maxime-leblan/Projet-E3-2026-ESIEE-Paris/Rapport/Exemple de document LateX/Code_TIPE/main.pdf

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

7 | mot = ""
8
9 | for i in range ( taille_mot - 1 , 0 , -1) :
10 | diviseur = b ** i
11 | quotient = dividende // diviseur
12 | mot += liste_int_a_char [ quotient ]
13 | dividende -= quotient * diviseur
14 | mot += liste_int_a_char [ dividende % b ]
15
16 | return mot
17
18 # Cré ation de l'exception " InvNotFound " utile dans la suite
19 | class InvNotFound ( Exception ) :
20 | pass
| Diapositive 38
1 | def inverse_mod ( b : int , n : int ) :
2 | """ Fonction qui prend en param ètre deux entiers b et n et renvoie l'
| inverse de b modulo n (ie b^( -1))
3 | ou bien renvoie l'erreur 'InvNotFound ' si b^( -1) n'existe pas """
4 | n_0 = n
5 | b_0 = b
6 | t_0 = 0
7 | t = 1
8 | q = int ( n_0 / b_0 )
9 | r = n_0 - q * b_0
10 | while r > 0:
11 | temp = t_0 - q * t
12 | if temp >= 0:
13 | temp = temp % n
14 | else :
15 | temp = n - (( - temp ) % n )
16 | t_0 = t
17 | t = temp
18 | n_0 = b_0
19 | b_0 = r
20 | q = int( n_0 / b_0 )
21 | r = n_0 - q * b_0
22 | if b_0 != 1:
23 | raise InvNotFound ()
24 | else :
25 | return t
| Diapositive 39
1 | def creation_cles ( lst_nb_prem : list ) :
2 | """ Fonction prenant en param ètre une liste de nombres premiers et qui crée
| puis renvoie un couple de la forme
3 | ( cle_publique , cle_privee ) en suivant la mé thode de cré ation des clés de l
| 'algorithme de chiffrement RSA\n
4 | - cle_publique : tuple int \n
5 | - cle_privee : int """
6 | e = 2
7 | # On choisit alé atoirement les valeurs de p et q distinctes
8 | p = lst_nb_prem . pop ( rd . randint (0 , len ( lst_nb_prem ) - 1) )
9 | q = rd . choice ( lst_nb_prem )
10 | # On choisit e et phi_n

11 | n = p * q
12 | phi_n = ( p - 1) * ( q - 1)
13
14 | for i in range (2 , phi_n ) : # on cherche le premier e qui convient en partant
| de e = 2
15 | if fu . pgcd (i , phi_n ) == 1:
16 | e = i
17 | break
18 | d = inverse_mod (e , phi_n )
19
20 | return (( n , e ) , d ) # on renvoie (clé publique , clé priv ée)
| Diapositive 40
1 | def chiffrer_RSA_naif ( m : int , cle_pb : tuple ) :
2 | """ Fonction qui prend en param ètre un entier m qui correspond au message à
| chiffrer et un tuple cle_pb qui
3 | correspond à la clé de chiffrement . Elle renvoie un entier correspondant au
| message chiffr é """
4
5 | assert ( m < cle_pb [0])
6 | # print ("début calcul chiffrement et cle_pb : " , cle_pb )
7 | reste = 1
8 | for _ in range ( cle_pb [1]) :
9 | reste *= m
10 | reste = reste % cle_pb [0]
11 | return reste
12
13 | def chiffrer_RSA_v2 ( m : int , cle_pb : tuple ) :
14 | """ Fonction qui prend en param ètre un entier m qui correspond au message à
| chiffrer et un tuple cle_pb qui
15 | correspond à la clé de chiffrement . Elle renvoie un entier correspondant au
| message chiffr é """
16
17 | assert ( m < cle_pb [0])
18 | return modulo_exp (m , cle_pb [1] , cle_pb [0])
| Diapositive 41
1 | def dechiffrer_RSA_naif ( x : int , cle_pv : int , n : int) :
2 | """ Fonction prenant en param ètre un entier x correspondant au message à dé
| chiffrer , cle_pv un entier
3 | correspondant à la clé de dé chiffrement et n issue de la cle de chiffrement
| du message . Elle renvoie un entier
4 | correspondant au message dé chiffr é """
5
6 | reste = 1
7 | for _ in range ( cle_pv ) :
8 | reste *= x
9 | reste = reste % n
10
11 | return reste
12
13 | def dechiffrer_RSA_v2 ( x : int , cle_pv : int , n : int) :
14 | """ Fonction prenant en param ètre un entier x correspondant au message à dé
| chiffrer , cle_pv un entier
15 | correspondant à la clé de dé chiffrement et n issue de la cle de chiffrement
| du message . Elle renvoie un entier

16 | correspondant au message dé chiffr é """
17
18 | return modulo_exp (x , cle_pv , n )
| Diapositive 42
1 | def chiffrer_chaine_RSA ( chaine :str , cle_pb :tuple , taille_facteur = -1) :
2 | """ Fonction qui prend en param ètre une chaine de caract ères 'chaine ' et un
| tuple 'cle_pb ' et renvoie
3 | une liste d'entiers correspondants aux facteurs de taille ' taille_facteur ',
| chiffr és avec la fonction ' chiffrer_RSA (...) ',
4 | dont la concat é nation forme la chaine 'chaine ' avant son chiffrement """
5 | if taille_facteur == ( -1) :
6 | taille_facteur = len ( chaine )
7 | chaine_chiffree = []
8 | chaine_fractionnee = []
9 | chaine_courante = ""
10
11 | for i in range (len( chaine ) ) : # On dé compose 'chaine ' en une liste de
| facteurs de taille ' taille_facteur '
12 | chaine_courante += chaine [ i ]
13 | if len( chaine_courante ) % taille_facteur == 0:
14 | chaine_fractionnee . append ( chaine_courante )
15 | chaine_courante = ""
16
17 | if chaine_courante != "":
18 | for i in range (len( chaine_courante ) , taille_facteur ) : # on ajoute des
| espaces pour que le dernier facteur soit de taille taille_facteur
19 | chaine_courante += " "
20 | chaine_fractionnee . append ( chaine_courante ) # on ajoute le dernier
| facteur de taille < ' taille_facteur ' ( sans compter les espaces )
21
22 | for facteur in chaine_fractionnee : # On chiffre tous les facteurs avec la
| fonction ' chiffrer_RSA (...) '
23 | int_facteur_courant = string_to_int ( facteur , base =95)
24 | chaine_chiffree . append ( chiffrer_RSA_v2 ( int_facteur_courant , cle_pb ) )
25 | return chaine_chiffree
| Diapositive 43
1 | def dechiffrer_chaine_RSA ( liste :list , cle_pv : int , n : int , taille_entiers =1) :
2 | """ Fonction qui prend en param ètre une liste d'entiers 'liste ', un entier
| 'cle_pv ' et un entier n et
3 | renvoie la concat é nation des chaines de caract ères dé chiffr ées avec '
| dechiffrer_RSA (...) ' à partir des entiers
4 | contenu dans 'liste ' repr é sentant des chaines de caract è res de taille '
| taille_entiers ' """
5
6 | chaine_dechiffree = ""
7
8 | for i in range (len( liste ) ) : # On dé chiffre tous les termes de liste sauf le
| dernier
9 | chaine_courante = int_to_string ( dechiffrer_RSA_v2 ( liste [ i ] , cle_pv , n ) ,
| taille_entiers , b =95)
10 | chaine_dechiffree += chaine_courante
11
12 | return chaine_dechiffree

Diapositive 44

1 | def aux_bytesub ( a : str) :
2 | """ Fonction auxiliaire de bytesub qui prend en entr ée un élé ment codé en
| hexad é cimal et renvoie le ré sultat
3 | de la fonction ByteSub appliqu ée à celui -ci """
4
5 | # on construit b_prime = GF(a)
6 | m_gf_i = m_gf_hex_a_dec [ a [0]]
7 | m_gf_j = m_gf_hex_a_dec [ a [1]]
8 | b_prime = MATRICE_GF [ m_gf_i ][ m_gf_j ]
9 | # on construit b à partir de b_prime
10 | b_prime = int( b_prime , 16)
11 | b_prime = str(bin( b_prime ) )
12 | b_prime = b_prime [2:]
13 | b_prime = fu . remplir_zeros ( b_prime , 8)
14 | b_prime = [[ int( b_prime [ i ]) ] for i in range (len( b_prime ) ) ]
15 | b = fu . produit_matriciel ( mat_f1 , b_prime , ( len ( mat_f1 ) , len( mat_f1 ) ) , (len(
| b_prime ) , 1) )
16 | b = fu . somme_matricielle (b , mat_f2 , len( mat_f2 ) , 1)
17 | for i in range (len( b ) ) :
18 | b [ i ][0] = b [ i ][0] % 2
19 | b_final = ""
20 | for chiffre in b :
21 | b_final += str( chiffre [0])
22 | b_final = fu . remplir_zeros ( b_final , 8)
23 | b_final = fu . bin_vers_dec ( b_final )
24 | b_final = str(hex( b_final ) )
25
26 | return b_final [2:]
| Diapositive 45
1 | def bytesub ( matrice : list [ list ]) :
2 | """ Fonction bytesub qui prend en entr ée une matrice cod ée en hexad é cimal
| et renvoie le ré sultat
3 | de la fonction aux_bytesub de AES appliqu ée à celle -ci """
4
5 | return [[ aux_bytesub ( matrice [ i ][ j ]) for j in range (len ( matrice ) ) ] for i in
| range (len( matrice ) ) ]
6
7 | def shiftrows ( matrice : list [ list ]) :
8 | """ Fonction qui applique la fonction ShiftRows de AES sur la matrice """
9 | n = len ( matrice )
10 | matrice_finale = []
11 | for d in range ( n ) :
12 | matrice_finale . append ( fu . decale_liste ( matrice [ d ] , d ) )
13
14 | return matrice_finale
| Diapositive 46

1 # Algorithme AES impl é ment é avec une biblioth èque
2 | def chiffrer_AES ( message :str , cle : bytes , vecteur : bytes ) :
3 | """ Fonction qui prend en param ètre un message , une clé et un vecteur et
| renvoie une chaine de
4 | caract ère correspondant au chiffrement de 'message ' avec l'algorithme AES
| en utilisant la clé 'cle '

5 | et le vecteur d' initialisation 'vecteur '\n
6 | - message : chaine de caract ères \n
7 | - cle : chaine de caract è res sur 32 octets \n
8 | - vecteur : chaine de caract ères sur 16 octets """
9
10 | padder = padding . PKCS7 (128) . padder ()
11 | padded_data = padder . update ( message . encode ('utf -8 ') )
12 | padded_data += padder . finalize ()
13
14 | cipher = Cipher ( algorithms . AES ( cle ) , modes . CBC ( vecteur ) , backend =
default_backend () )
15 | encryptor = cipher . encryptor ()
16 | message_chiffre = encryptor . update ( padded_data ) + encryptor . finalize ()
17
18 | return message_chiffre

Diapositive 47

1 | def dechiffrer_AES ( message_chiffre , cle : bytes , vecteur : bytes ) :
2 | """ Fonction qui prend en param ètre un message , une clé et un vecteur et
renvoie une chaine de
3 | caract ère correspondant au dé chiffrement de ' message_chiffre ' avec l'
algorithme AES en utilisant la clé 'cle '
4 | et le vecteur d' initialisation 'vecteur '\n
5 | - message_chiffre : chaine de caract ères\n
6 | - cle : chaine de caract è res sur 32 octets \n
7 | - vecteur : chaine de caract ères sur 16 octets """
8
9 | decryptor = Cipher ( algorithms . AES ( cle ) , modes . CBC ( vecteur ) , backend =
default_backend () ) . decryptor ()
10 | decrypted_data = decryptor . update ( message_chiffre ) + decryptor . finalize ()
11
12 | unpadder = padding . PKCS7 (128) . unpadder ()
13 | unpadded_data = unpadder . update ( decrypted_data )
14 | unpadded_data += unpadder . finalize ()
15
16 | return unpadded_data . decode ('utf -8 ')

Diapositive 48

3 | serveur.py
1 | class Serveur :
2 | """ Classe permettant de simuler un serveur informatique simplifi é à l'aide
du module socket """
3
4 | def __init__ ( self , modele :int , port =6390) :
5 | self . host = ""
6 | self . port = port
7 | self . socket = None
8 | self . clients = []
9 | self . threads = {}
10 | self . id_client = 1
11 | self . arret = False
12 | self . modele = modele
13
14 | def close ( self ) :

15 | """ Fonction qui vé rifie si le serveur doit s'é teindre ou non """
16 | while True :
17 | if self . arret == True :
18 | break
| Diapositive 49
1 | def connections ( self ) :
2 | """ Fonction qui gère les connexions au serveur d'é ventuels clients en
| temps réel """
3 | while True :
4 | client , ip = self . socket . accept ()
5 | self . clients . append (( self . id_client , client , ip ) )
6 | # on lance un fil d'exé cution pour chaque nouveau client afin de
| pouvoir recevoir ses messages
7 | # on choisit la bonne fonction de ré ception en fonction du mod èle
| utilis é
8 | if self . modele != 3:
9 | self . threads [str ( self . id_client ) ] = threading . Thread ( target =
| self . reception , args =[ client , self . id_client ])
10 | else :
11 | self . threads [str ( self . id_client ) ] = threading . Thread ( target =
| self . reception_cm , args =[ client , self . id_client ])
12 | self . threads [str( self . id_client ) ]. start ()
13
14 | print ("Le client ", self . id_client , " d'adresse ", ip , " s'est
| connect é")
15 | self . id_client += 1
16
17 | def transfert ( self , expediteur :str , destinataire , message :str , separateur ="
| :") :
18 | """ Fonction qui transfert un message entre 2 clients """
19 | new_msg = "<Client -" + expediteur + ">" + separateur + message
20 | destinataire . send ( new_msg . encode ("utf -8") )
| Diapositive 50
1 | def reception ( self , client , id_client :int ) :
2 | """ Fonction qui ré ceptionne les requ ê tes des clients et qui les traite
| pour les modè les 1 et 2"""
3 | while True :
4 | requete_client = client . recv (500)
5 | requete_client = requete_client . decode ("utf -8")
6 | print ("<Client -" + str( id_client ) + " >:", requete_client )
7 | print () # on passe une ligne pour aérer l'affichage
8 | if requete_client == "/S -close ":
9 | print (" CLOSE ")
10 | self . arret = True
11 | else : # on envoie le message au bon destinataire en fonction de l'
| expé diteur
12 | if id_client == 1:
13 | self . transfert (str( id_client ) , self . clients [1][1] ,
| requete_client , separateur ="|")
14 | else :
15 | self . transfert (str( id_client ) , self . clients [0][1] ,
| requete_client , separateur ="|")
| Diapositive 51

1 | def reception_cm ( self , client , id_client :int ) :
2 | """ Fonction qui ré ceptionne les requ ê tes des clients et qui les traite
| pour le modèle 3 """
3 | while True :
4 | requete_client = client . recv (500)
5 | requete_client = requete_client . decode ("utf -8")
6 | decomp_msg = fu . decomposition_chaine ( requete_client , separateur ="|"
| )
7 | print ("<Client -" + str( id_client ) + " >:", requete_client )
8 | print () # on passe une ligne pour aérer l'affichage
9 | if requete_client == "/S -close ":
10 | print (" CLOSE ")
11 | self . arret = True
12 | elif "/S -check " in requete_client :
13 | if id_client == 1:
14 | destinataire = 1
15 | else :
16 | destinataire = 0
17 | self . transfert (str ( id_client ) , self . clients [ destinataire ][1] ,
| requete_client , separateur ="|")
| Diapositive 52
1 | elif "/S -init " in requete_client :
2 | if len( decomp_msg ) > 2: # si le client malveillant veut envoyer
| une clé altérée
3 | # on l'envoie au bon destinataire
4 | expediteur = decomp_msg [2]
5 | destinataire = int( decomp_msg [3]) - 1
6 | # on supprime les infos concernant l'exp é diteur et le
| destinataire
7 | decomp_msg . pop ()
8 | decomp_msg . pop ()
9 | requete_client = fu . compression_arg_str ( decomp_msg ,
| separateur ="|")
10 | self . transfert ( expediteur , self . clients [ destinataire ][1] ,
| requete_client , separateur ="|")
11 | else : # sinon c'est la clé d'origine d'un client normal
12 | # on envoie donc sa clé au client malveillant
13 | self . transfert (str( id_client ) , self . clients [2][1] ,
| requete_client , separateur ="|")
14 | elif id_client != 3: # si le serveur reçoit un message d'un client
| normal
15 | # on l'envoit au client malveillant
16 | self . transfert (str ( id_client ) , self . clients [2][1] ,
| requete_client , separateur ="|")
17 | else :
18 | # on l'envoie au bon destinataire
19 | expediteur = decomp_msg [4]
20 | destinataire = int( decomp_msg [5]) - 1
21 | # on supprime les infos concernant l'expé diteur et le
| destinataire
22 | decomp_msg . pop ()
23 | decomp_msg . pop ()
24 | requete_client = fu . compression_arg_str ( decomp_msg , separateur =
| "|")
25 | self . transfert ( expediteur , self . clients [ destinataire ][1] ,

requete_client , separateur ="|")

Diapositive 53

1 | def run ( self ) :
2 | """ Fonction qui dé marre et ferme le serveur """
3 | # cré ation du socket pour "dé marrer " le serveur
4 | self . socket = socket . socket ( socket . AF_INET , socket . SOCK_STREAM )
5 | self . socket . bind (( self . host , self . port ) )
6 | print ("Le serveur est dé marr é...")
7
8 | self . socket . listen (1) # on le met en mode ré cepteur
9
10 | connections = threading . Thread ( target = self . connections , args =[])
11 | connections . start ()
12
13 | execution = threading . Thread ( target = self . close , args =[])
14 | execution . start ()
15
16 | execution . join ()
17
18 | for client in self . clients :
19 | client [1]. close ()
20 | self . socket . close ()
| Diapositive 54
4 | client.py
1 | class Client_RSA :
2 | """ Classe permettant de simuler un client pouvant se connecter à un
serveur informatique simplifi é
3 | à l'aide du module socket , qui base le chiffrement sur l'algorithme du RSA
"""
4
5 | def __init__ ( self , id: int , liste_nb_premiers , host =" localhost ", port =6390)
:
6 | self .id = id
7 | self . host = host
8 | self . port = port
9 | self . socket = None
10 | self . cle_pv_RSA = None
11 | self . cle_pb_RSA = None
12 | self . cles_pb_RSA_autres = {}
13 | self . liste_nb_premiers = liste_nb_premiers
14 | self . init_envoi = False # permet de savoir si self . initialisation_RSA ()
a déjà été exécutée dans self . envoyer ()
15 | self . init_recu = False | # permet de savoir si self . initialisation_RSA ()
a déjà été exécutée dans self . reception ()
16 | # messages envoy és de la forme : " Client_X : taille_msg : message_chiffre "
17 | # On renomme les indices que l'on utilise dans le code pour pouvoir les
modifier plus facilement
18 | # et pour plus de visibilit é
19 | self . i_client = 0
20 | self . i_taille_msg = 1
21 | self . i_msg_chiffre = 2

Diapositive 55

1 | def initialisation_RSA ( self , message : str , separateur ="|") :
2 | """ Fonction qui crée la clé priv ée et la clé publique du client pour l
| 'algo de chiffrement RSA.
3 | Elle est exécutée à l' initialisation de la connection avec le serveur
| et partage la clé publique du client
4 | avec un autre client connect é au serveur avec lequel il veut
| communiquer ."""
5
6 | cles = algos . creation_cles ( self . liste_nb_premiers )
7 | self . cle_pb_RSA = cles [0]
8 | self . cle_pv_RSA = cles [1]
9 | msg = fu . compression_arg_str ([ self . cle_pb_RSA [0] , self . cle_pb_RSA [1]])
10 | msg = message + separateur + msg
11
12 | return msg
13
14 | def envoyer ( self , socket ) :
15 | """ Fonction permettant d'envoyer un message à un client en passant par
| le serveur """
16 | try:
17 | while True :
18 | msg = input (" -->")
19 | if msg == "/S -init " and not self . init_envoi :
20 | socket . send ( self . initialisation_RSA ( msg ) . encode ("utf -8") )
21 | self . init_envoi = True
22 | elif msg == "/S -close ":
23 | socket . send ( msg . encode ("utf -8") )
| Diapositive 56
1 | else :
2 | try :
3 | if self .id == 1: # on chiffre le message avec la clé
| publique du bon client
4 | # msg_chiffre = algos . chiffrer_RSA ( algos .
| string_to_int ( msg ), self . cles_pb_RSA_autres
| ["2"])
5 | msg_chiffre = algos . chiffrer_chaine_RSA ( msg , self .
| cles_pb_RSA_autres ["2"] , taille_facteur =3)
6 | else :
7 | # msg_chiffre = algos . chiffrer_RSA ( algos .
| string_to_int ( msg ), self . cles_pb_RSA_autres
| ["1"])
8 | msg_chiffre = algos . chiffrer_chaine_RSA ( msg , self .
| cles_pb_RSA_autres ["1"] , taille_facteur =3)
9 | # on transforme le message sous forme de liste en
| chaine de caract ères
10 | msg_chiffre = fu . compression_arg_str ( msg_chiffre )
11 | msg_envoye = str(len( msg ) ) + "|" + str( msg_chiffre ) #
| on ajoute la longueur du message chiffr é au message
| envoy é
12 | msg_envoye = msg_envoye . encode ("utf -8")
13 | socket . send ( msg_envoye )
14 | except AssertionError :
15 | print (" Erreur lors de la tentative de chiffrement du
| message . Veuillez essayer à nouveau ")

16 | except ConnectionResetError :
17 | print ("Dé connexion du serveur ... ")
18 | sys . exit ()
| Diapositive 57
1 | def reception ( self , socket ) :
2 | """ Fonction qui ré ceptionne les messages reçus du serveur """
3 | try:
4 | while True :
5 | requete_serveur = socket . recv (500)
6 | requete_serveur = requete_serveur . decode ("utf -8")
7 | # requete_serveur est de la forme : " Client_X : taille_msg :
| message_chiffre "
8 | decomp_msg = fu . decomposition_chaine ( requete_serveur )
9 | id_expediteur = fu . id_client ( requete_serveur )
10
11 | if "/S -init " in decomp_msg and not self . init_recu : # si on a
| pas enregistr é les clés publiques de l'autre client , on le
| fait
12 | self . cles_pb_RSA_autres [ id_expediteur ] = fu .
| extraction_arg_str ( decomp_msg [ self . i_msg_chiffre ])
13 | self . init_recu = True
14 | if not self . init_envoi : # si on a pas é chang é notre clé
| publique , on le fait
15 | socket . send ( self . initialisation_RSA ("/S -init ") . encode (
| "utf -8") )
16 | self . init_envoi = True
| Diapositive 58
1 | else :
2 | taille_msg = int ( decomp_msg [ self . i_taille_msg ])
3 | # on reconvertit le message chiffr é (str ) en liste d'
| entiers pour pouvoir ensuite le dé chiffrer
4 | msg_chiffre = fu . extraction_arg_str ( decomp_msg [ self .
| i_msg_chiffre ])
5 | # on vé rifie qui est l'expé diteur pour prendre sa clé
| publique correspondante
6 | if id_expediteur == 1:
7 | # msg_dechiffre = algos . dechiffrer_RSA (int ( decomp_msg
| [2]) , self . cle_pv_RSA , self . cle_pb_RSA [0])
8 | msg_dechiffre = algos . dechiffrer_chaine_RSA ( msg_chiffre
| , self . cle_pv_RSA , self . cle_pb_RSA [0] ,
| taille_entiers =3)
9 | else :
10 | msg_dechiffre = algos . dechiffrer_chaine_RSA ( msg_chiffre
| , self . cle_pv_RSA , self . cle_pb_RSA [0] ,
| taille_entiers =3)
11 | print ("\n", decomp_msg [ self . i_client ] + ":" + msg_dechiffre
| )
12 | print ("\n- - >", end ="")
13 | except ConnectionResetError :
14 | print (" Connexion interrompue \nSi le terminal est en attente ,
| appuyez sur Entr ée")
15 | sys . exit ()
| Diapositive 59

1 | def connection ( self ) :
2 | """ Fonction permettant de connecter le client à un serveur """
3 | self . socket = socket . socket ( socket . AF_INET , socket . SOCK_STREAM )
4 | self . socket . connect (( self . host , self . port ) )
5 | envoi = threading . Thread ( target = self . envoyer , args =[ self . socket ])
6 | recep = threading . Thread ( target = self . reception , args =[ self . socket ])
7 | envoi . start ()
8 | recep . start ()
9
10 | class Client_AES_RSA ( Client_RSA ) :
11 | """ Classe fille de Client_RSA permettant de simuler un client pouvant se
| connecter à un serveur informatique simplifi é
12 | à l'aide du module socket , qui base le chiffrement sur une combinaison de l
| 'algorithme RSA et AES """
13 | def __init__ ( self , id: int , liste_nb_premiers ) :
14 | Client_RSA . __init__ ( self , id , liste_nb_premiers )
15 | # messages envoy és de la forme : " Client_X | taille_msg | cle_AES | vect_AES |
| message_chiffre "
16 | # On renomme les indices que l'on utilise dans le code pour pouvoir les
| modifier plus facilement
17 | # et pour plus de visibilit é
18 | self . i_client = 0
19 | self . i_taille_msg = 1
20 | self . i_cle_AES = 2
21 | self . i_vect_AES = 3
22 | self . i_msg_chiffre = 4
| Diapositive 60
1 | def envoyer ( self , socket ) :
2 | """ Fonction permettant d'envoyer un message à un client en passant par
| le serveur """
3 | try:
4 | while True :
5 | msg = input (" -->")
6 | if msg == "/S -init " and not self . init_envoi :
7 | # on envoie notre clé publique à l'autre client
8 | socket . send ( self . initialisation_RSA ( msg , separateur ="|") .
| encode ("utf -8") )
9 | self . init_envoi = True
10 | elif msg == "/S -close ":
11 | socket . send ( msg . encode ("utf -8") )
12 | elif msg == "/S -check ":
13 | # on construit le hash de la clé publique de l'expé diteur
| et on l'envoie à l'autre client
14 | cle_pb = str ( self . cle_pb_RSA [0]) + "/" + str( self .
| cle_pb_RSA [1])
15 | hash_cle = hashlib . sha256 ( cle_pb . encode () )
16 | hash_cle = hash_cle . hexdigest ()
17 | msg += "|" + hash_cle
18 | socket . send ( msg . encode () )
19 | else :
20 | try :
21 | cle_AES = fu . generateur_alea_chaine (32)
22 | vecteur_AES = fu . generateur_alea_chaine (16)
23 | # si on veut envoyer un msg au client 1 , on chiffre
| avec la clé publique du client 2

24 | if self .id == 1: | # on chiffre le message avec la clé
publique du bon client
25 | destinataire = "2"

Diapositive 61

1 | else : # sinon c'est l'inverse
2 | destinataire = "1"
3 | # On chiffre le message avec la cle et le vecteur AES
4 | msg_chiffre = algos . chiffrer_AES ( msg , fu . encode_ascii (
cle_AES ) , fu . encode_ascii ( vecteur_AES ) )
5 | msg_chiffre = msg_chiffre . decode ("latin -1")
6 | # On chiffre la cle et le vecteur pour AES avec le RSA
7 | cle_AES = algos . chiffrer_chaine_RSA ( cle_AES , self .
cles_pb_RSA_autres [ destinataire ] , taille_facteur =4)
8 | vecteur_AES = algos . chiffrer_chaine_RSA ( vecteur_AES ,
self . cles_pb_RSA_autres [ destinataire ] , taille_facteur =4)
9 | # on transforme le message , la clé et le vecteur sous
forme de liste en chaine de caract ères
10 | msg_chiffre = fu . compression_arg_str ([ msg_chiffre ])
11 | cle_AES = fu . compression_arg_str ( cle_AES )
12 | vecteur_AES = fu . compression_arg_str ( vecteur_AES )
13 | # On construit le message que l'on va envoyer contenant
toutes les infos né cessaires pour le destinataire
14 | msg_envoye = str(len( msg ) ) + "|" + cle_AES + "|" +
vecteur_AES + "|" + msg_chiffre
15 | msg_envoye = msg_envoye . encode ("utf -8")
16 | socket . send ( msg_envoye )
17 | except AssertionError :
18 | print (" Erreur lors de la tentative de chiffrement du
message . Veuillez essayer à nouveau ")
19 | except ConnectionResetError :
20 | print ("Dé connexion du serveur ... ")
21 | sys . exit ()

Diapositive 62

1 | def reception ( self , socket ) :
2 | """ Fonction qui ré ceptionne les messages reçus du serveur """
3 | try:
4 | while True :
5 | requete_serveur = socket . recv (500)
6 | requete_serveur = requete_serveur . decode ("utf -8")
7 | decomp_msg = fu . decomposition_chaine ( requete_serveur ,
separateur ="|")
8 | id_expediteur = fu . id_client ( requete_serveur )
9 | if "/S -init " in decomp_msg and not self . init_recu : | # si on a
pas enregistr é les clés publiques de l'autre client , on le fait
10 | self . cles_pb_RSA_autres [ id_expediteur ] = fu .
extraction_arg_str ( decomp_msg [2])
11 | self . init_recu = True
12 | if not self . init_envoi : | # si on a pas é chang é notre clé
publique , on le fait
13 | socket . send ( self . initialisation_RSA ("/S -init ",
separateur ="|") . encode ("utf -8") )
14 | self . init_envoi = True

15 | elif "/S -check " in requete_serveur :
16 | print ("\ nComparaison des clés en cours ...")
17 | # on construit le hash de la clé de l'autre client à partir
| de notre base de donn ée
18 | cle_pb = str ( self . cles_pb_RSA_autres [ id_expediteur ][0]) + "
| /" + str( self . cles_pb_RSA_autres [ id_expediteur ][1])
19 | hash_cle = hashlib . sha256 ( cle_pb . encode () )
20 | hash_cle = hash_cle . hexdigest ()
21 | # on ré cupère le hash envoy é par l'autre client
22 | hash_autre_cle = decomp_msg [ -1]
| Diapositive 63
1 | if hash_autre_cle != hash_cle :
2 | print ("La communication n'est plus sé curis ée /!\ ")
3 | else :
4 | print ("La communication est sé curis ée")
5 | else :
6 | # On extrait et dé chiffre la clé et le vecteur AES
7 | cle_AES = fu . extraction_arg_str ( decomp_msg [ self . i_cle_AES ])
8 | cle_AES = algos . dechiffrer_chaine_RSA ( cle_AES , self .
| cle_pv_RSA , self . cle_pb_RSA [0] , taille_entiers =4)
9 | vecteur_AES = fu . extraction_arg_str ( decomp_msg [ self .
| i_vect_AES ])
10 | vecteur_AES = algos . dechiffrer_chaine_RSA ( vecteur_AES , self
| . cle_pv_RSA , self . cle_pb_RSA [0] , taille_entiers =4)
11
12 | # on ré cupère le message chiffr é et on le dé chiffre
13 | msg_chiffre = decomp_msg [ self . i_msg_chiffre ]
14 | msg_chiffre = msg_chiffre . encode ("latin -1")
15 | msg_dechiffre = algos . dechiffrer_AES ( msg_chiffre , fu .
| encode_ascii ( cle_AES ) , fu . encode_ascii ( vecteur_AES ) )
16 | print ("\n", decomp_msg [ self . i_client ] + ":" + msg_dechiffre
| )
17 | print ("\n- - >", end ="")
18 | except ConnectionResetError :
19 | print (" Connexion interrompue \nSi le terminal est en attente ,
| appuyez sur Entr ée")
20 | sys . exit ()
| Diapositive 64
1 | class ClientMalveillant ( Client_AES_RSA ) :
2 | """ Classe fille de la classe Client_AES_RSA qui initialise le client
| malveillant voulant lire des conversations
3 | sé curis ées entre les autres clients connect és au même serveur , dans le
| cadre du modèle n 3 avec la fonction
4 | de hachage et le canal secret """
5 | def __init__ ( self , id: int , liste_nb_premiers ) :
6 | Client_AES_RSA . __init__ ( self , id , liste_nb_premiers )
7 | # Compteur indiquant le nombre d'é changes de clés que le Client
| Malveillant a effectu é avec les autres clients
8 | self . nb_cles_echangees = 0
9
10 | def initialisation_RSA ( self , message : str , separateur ="|", expediteur ="",
| destinataire ="") :
11 | """ Fonction qui crée la clé priv ée et la clé publique du client pour l
| 'algo de chiffrement RSA.

12 | Elle est exécutée à l' initialisation de la connection avec le serveur
et partage la clé publique du client
13 | avec un autre client connect é au serveur avec lequel il veut
communiquer ."""
14 | if self . cle_pv_RSA == None : # si on a pas encore créé nos clés, on le
fait
15 | cles = algos . creation_cles ( self . liste_nb_premiers )
16 | self . cle_pb_RSA = cles [0]
17 | self . cle_pv_RSA = cles [1]
18 | msg = fu . compression_arg_str ([ self . cle_pb_RSA [0] , self . cle_pb_RSA [1]])
19 | print ("clé envoy ée : ", msg )
20 | msg = fu . compression_arg_str ([ msg , expediteur , destinataire ] ,
| separateur ="|")
21 | msg = message + separateur + msg
22 | return msg

Diapositive 65

1 | def reception ( self , socket ) :
2 | """ Fonction qui ré ceptionne les messages reçus du serveur """
3 | try:
4 | while True :
5 | requete_serveur = socket . recv (500)
6 | requete_serveur = requete_serveur . decode ("utf -8")
7 | decomp_msg = fu . decomposition_chaine ( requete_serveur ,
| separateur ="|")
8 | id_expediteur = fu . id_client ( requete_serveur )
9
10 | if "/S -init " in decomp_msg : | # si on reçoit une clé publique ,
| on l'enregistre
11 | self . cles_pb_RSA_autres [ id_expediteur ] = fu .
extraction_arg_str ( decomp_msg [2])
12 | print ("clé reçue : ", fu . extraction_arg_str ( decomp_msg [2]) )
13 | # on envoie notre propre clé publique au bon destinataire
14 | if id_expediteur == "1":
15 | socket . send ( self . initialisation_RSA ("/S -init ",
separateur ="|", expediteur = id_expediteur , destinataire ="2") . encode ("utf -8") )
16 | else :
17 | socket . send ( self . initialisation_RSA ("/S -init ",
separateur ="|", expediteur = id_expediteur , destinataire ="1") . encode ("utf -8") )

Diapositive 66

1 | else :
2 | # On extrait et dé chiffre la clé et le vecteur AES
3 | cle_AES = fu . extraction_arg_str ( decomp_msg [ self . i_cle_AES ])
4 | cle_AES = algos . dechiffrer_chaine_RSA ( cle_AES , self .
cle_pv_RSA , self . cle_pb_RSA [0] , taille_entiers =4)
5 | vecteur_AES = fu . extraction_arg_str ( decomp_msg [ self .
| i_vect_AES ])
6 | vecteur_AES = algos . dechiffrer_chaine_RSA ( vecteur_AES , self
. cle_pv_RSA , self . cle_pb_RSA [0] , taille_entiers =4) 7
8 | # on ré cup ère le message chiffr é et on le dé chiffre
9 | msg_chiffre = decomp_msg [ self . i_msg_chiffre ]
10 | msg_chiffre = msg_chiffre . encode ("latin -1")

11 | msg_dechiffre = algos . dechiffrer_AES ( msg_chiffre , fu .
encode_ascii ( cle_AES ) , fu . encode_ascii ( vecteur_AES ) )
12 | print ("\n", decomp_msg [ self . i_client ] + ":" + msg_dechiffre
)
13
14 | # on renvoie le message au destinataire chiffr é avec la clé
publique du destinataire
15 | # si on veut envoyer un msg au client 1 , on chiffre avec la
clé publique du client 2
16 | if id_expediteur == "1": | # on chiffre le message avec la
clé publique du bon client
17 | destinataire = "2"
18 | else : | # sinon c'est l'inverse
19 | destinataire = "1"

Diapositive 67

1 | # On chiffre le message avec la cle et le vecteur AES
2 | msg_chiffre = algos . chiffrer_AES ( msg_dechiffre , fu .
encode_ascii ( cle_AES ) , fu . encode_ascii ( vecteur_AES ) )
3 | msg_chiffre = msg_chiffre . decode ("latin -1")
4 | # On chiffre la cle et le vecteur pour AES avec le RSA
5 | cle_AES = algos . chiffrer_chaine_RSA ( cle_AES , self .
cles_pb_RSA_autres [ destinataire ] , taille_facteur =4)
6 | vecteur_AES = algos . chiffrer_chaine_RSA ( vecteur_AES , self .
cles_pb_RSA_autres [ destinataire ] , taille_facteur =4)
7 | # on transforme le message , la clé et le vecteur sous forme
de liste en chaine de caract ères
8 | msg_chiffre = fu . compression_arg_str ([ msg_chiffre ])
9 | cle_AES = fu . compression_arg_str ( cle_AES )
10 | vecteur_AES = fu . compression_arg_str ( vecteur_AES )
11 | # On construit le message que l'on va envoyer contenant
toutes les infos né cessaires pour le destinataire
12 | msg_envoye = str (len( msg_dechiffre ) ) + "|" + cle_AES + "|"
+ vecteur_AES + "|" + msg_chiffre + "|" + id_expediteur + "|" + destinataire
13 | msg_envoye = msg_envoye . encode ("utf -8")
14 | socket . send ( msg_envoye )
15 | except ConnectionResetError :
16 | print (" Connexion interrompue \nSi le terminal est en attente ,
appuyez sur Entr ée")
17 | sys . exit ()
18
19 | def connection ( self ) :
20 | """ Fonction permettant de connecter le client à un serveur """
21 | self . socket = socket . socket ( socket . AF_INET , socket . SOCK_STREAM )
22 | self . socket . connect (( self . host , self . port ) )
23 | recep = threading . Thread ( target = self . reception , args =[ self . socket ])
24 | recep . start ()

Diapositive 68

5 | fonctions_utiles.py
1 | def copie_dict ( dico : dict ) :
2 | """ Fonction qui renvoie une copie indé pendante du dictionnaire 'dico ' """
3 | dico_copie = {}

4 | for cle , valeur in dico . items () :
5 | dico_copie [ cle ] = valeur
6
7 | return dico_copie
8
9 | def pgcd ( a : int , b : int) :
10 | """ Fonction qui prend en param ètre 2 entiers naturel a et b et renvoie
| leur PGCD """
11
12 | dividende = max(a , b )
13 | diviseur = min(a , b )
14 | temp = 0
15 | while ( dividende % diviseur ) != 0 :
16 | temp = dividende % diviseur
17 | dividende = diviseur
18 | diviseur = temp
19
20 | return diviseur
| Diapositive 69
1 | def compression_arg_str ( liste_args : list , separateur ="/") :
2 | """ Fonction qui prend en param ètre une liste d'objets pouvant être
| convertis en chaine de caract ères , un sé parateur '/ ' et renvoie une
| chaine de caract ères contenant n param è tres et qui est de la forme 'arg
| [1]/ arg [2]/.../ arg[n] ' """
3 | arguments = ""
4 | for i in range (len( liste_args ) ) :
5 | if i != len( liste_args ) - 1:
6 | arguments += str( liste_args [ i ]) + separateur
7 | else :
8 | arguments += str( liste_args [ i ])
9 | return arguments
10
11 | def extraction_arg_str ( chaine_args : str , separateur ="/") :
12 | """ Fonction qui prend en param ètre une chaine de caract ères contenant n
| arguments et de la forme 'arg [1]/ arg [2]/.../ arg [n] ' , un sé parateur '/ '
| et renvoie une liste contenant les n arguments de type int"""
13 | chiffres = " 0123456789 "
14 | liste_args = []
15 | arg_courant = ""
16 | for i in range (len( chaine_args ) ) :
17 | if chaine_args [ i ] != separateur and chaine_args [ i ] in chiffres :
18 | arg_courant += chaine_args [ i ]
19 | else :
20 | liste_args . append ( int( arg_courant ) )
21 | arg_courant = ""
22 | if arg_courant != "":
23 | liste_args . append (int( arg_courant ) )
24 | return liste_args
| Diapositive 70
1 | def decomposition_chaine ( chaine : str , separateur ="|") :
2 | """ Fonction qui prend en param ètre une chaîne de caract ères que l'on peut
| diviser en sous -chaî nes sé par ées par un sé parateur ': ' et renvoie une
| liste contenant ces sous -chaînes """
3 | liste_sous_chaines = []

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

4 | chaine_finale = ""
5 | for _ in range ( n ) :
6 | chaine_finale += chaine
7
8 | return chaine_finale
9
10 | def encode_ascii ( chaine :str) :
11 | """ Fonction qui transforme une chaine str en bstr (ie en code ASCII )\n
12 | NB : elle fait la même chose que la fonction native bytes ( chaine , encoding =
| " ascii ") """
13
14 | return bytes ( chaine , encoding ="utf -8")
| Diapositive 73
1 | def matrice_gf ( chaine : str , taille =16) :
2 | """ Renvoie la matrice GF sous forme de matrice de type list [ list ] """
3 | matrice_gf = decomposition_chaine ( chaine , separateur =" ")
4 | matrice_gf_bis = []
5 | matrice_gf_finale = []
6 | ligne_gf = []
7
8 | for i in range (len( matrice_gf ) ) :
9 | if "\n" in matrice_gf [ i ]:
10 | matrice_gf_bis . append ( matrice_gf [ i ][:( -1) ])
11 | elif matrice_gf [ i ] != "":
12 | matrice_gf_bis . append ( matrice_gf [ i ])
13
14 | for i in range ( taille ) :
15 | for j in range ( taille ) :
16 | ligne_gf . append ( matrice_gf_bis [ i * taille + j ])
17 | if j == taille - 1:
18 | matrice_gf_finale . append ( ligne_gf )
19 | ligne_gf = []
20
21 | return matrice_gf_finale
| Diapositive 74
1 | def conversion_matrice ( matrice : list [ list ] , fonction , base =10) :
2 | """ Fonction qui applique la fonction de conversion 'fonction ' sur chaque
| case de la matrice carr ée """
3 | res = matrice . copy ()
4 | for i in range (len( matrice ) ) :
5 | for j in range ( len( matrice ) ) :
6 | if base != 10:
7 | res [ i ][ j ] = fonction ( res [ i ][ j ] , base )
8 | else :
9 | res [ i ][ j ] = fonction ( res [ i ][ j ])
10
11 | return res
| Diapositive 75
1 | def produit_matriciel ( m1 : list [ list [int ]] , m2 : list [ list [int ]] , n1 =( -1 , -1) , n2
| =( -1 , -1) ) :
2 | """ Fonction qui renvoie le produit matriciel des matrices m1 et m2 """
3 | assert ( n1 [1] == n2 [0])

4 | if n1 == ( -1 , -1) :
5 | n = len( m1 )
6 | p = n
7 | q = n
8 | else :
9 | n , p = n1 [0] , n1 [1]
10 | q = n2 [1]
11 | res = [[0 for _ in range ( q ) ] for _ in range ( n ) ]
12 | for i in range ( n ) :
13 | for j in range ( q ) :
14 | somme = 0
15 | for k in range ( p ) :
16 | somme += m1 [ i ][ k ] * m2 [ k ][ j ]
17 | res [ i ][ j ] = somme
18 | return res
19
20 | def somme_matricielle ( m1 : list [ list [int ]] , m2 : list [ list [ int ]] , n : int , p : int)
| :
21 | """ Fonction qui renvoie la somme des matrices m1 et m2 """
22 | res = [[0 for _ in range ( p ) ] for _ in range ( n ) ]
23 | for i in range ( n ) :
24 | for j in range ( p ) :
25 | res [ i ][ j ] = m1 [ i ][ j ] + m2 [ i ][ j ]
26 | return res
| Diapositive 76
1 | def bin_vers_dec ( x :str) :
2 | """ Fonction qui convertit un élé ment de type int binaire en élé ment de
| type int dé cimal """
3 | x_str = str( x )
4 | x_liste = [int( c ) for c in x_str ]
5 | x_liste . reverse ()
6 | x_int = 0
7 | k = 0
8 | for c in x_liste :
9 | x_int += 2** k * c
10 | k += 1
11
12 | return x_int
13
14 | def remplir_zeros (x , n : int ) :
15 | """ Rajoute des zé ros jusqu 'à ce que 'x' soit un nombre binaire codé sur n
| bits """
16 | x_str = str( x )
17 | while len( x_str ) < n :
18 | x_str = "0" + x_str
19
20 | return x_str
| Diapositive 77
1 | def affiche_matrice ( m : list [ list ]) :
2 | """ Fonction qui affiche une matrice carr ée """
3 | for i in range (len( m ) ) :
4 | for j in range ( len( m ) ) :
5 | print ( m [ i ][ j ] , " ", end ="")
6 | print ()

8 | def decale_liste ( liste : list , d : int) :
9 | """ Fonction qui dé cale les élé ments de la liste de 'd' vers la droite
10 | et renvoie le ré sultat """
11 | liste_bis = liste . copy ()
12 | liste_finale = []
13 | d_bis = d
14
15 | if d == 0:
16 | return liste
17
18 | while d_bis > 0:
19 | liste_finale = []
20 | liste_finale . append ( liste_bis . pop () )
21 | for el in liste_bis :
22 | liste_finale . append ( el )
23 | liste_bis = liste_finale . copy ()
24 | d_bis -= 1
25
26 | return liste_finale
| Diapositive 78
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
