maxime-leblan/Projet-E3-2026-ESIEE-Paris/Rapport/Exemple de document LateX/TIPE_MPI_2025___Sécurisation_réseau_ordinateurs/main.pdf

# Sécurisation des échanges d'informations entre deux ordinateurs

# Maxime LE BLAN

28798

Maxime LE BLAN | 28798 | 1 / 78

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

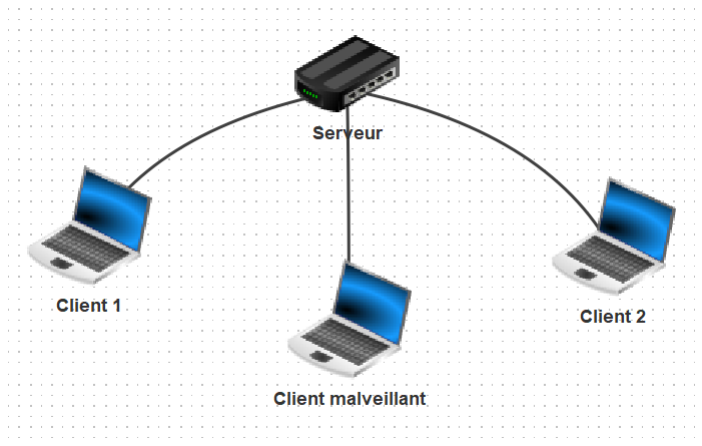
[picture p90: figure]

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

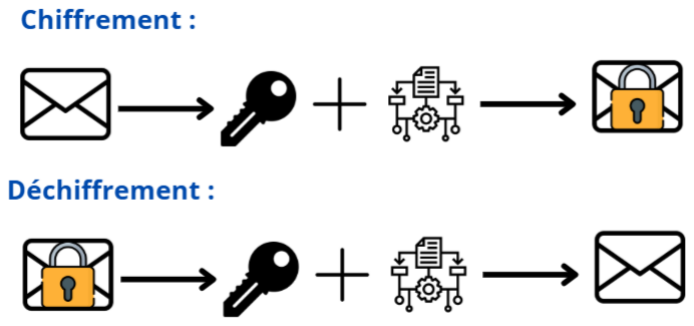
[picture p91: figure]

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

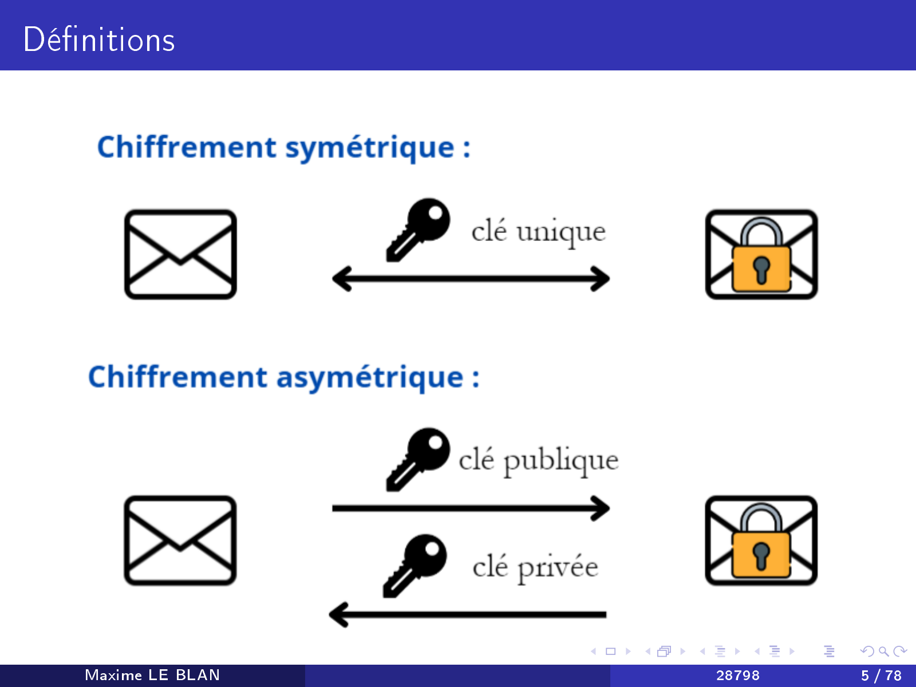
[picture p92: page 5]

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

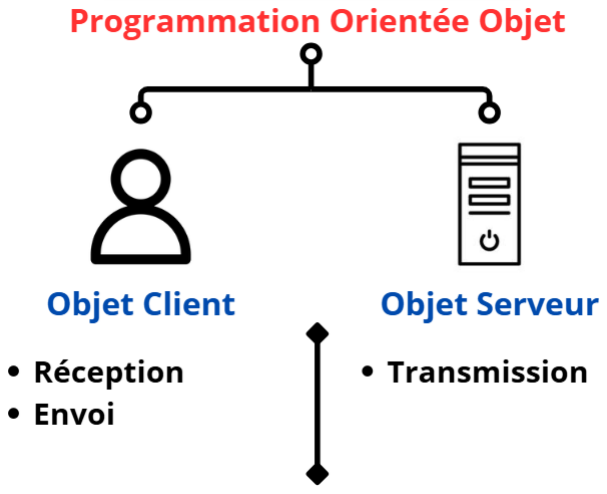
[picture p93: figure]

# Implémentation

1 | Problèmes :
| ▶ Programmation séquentielle ne permet pas d'envoyer et de recevoir des messages en même temps ▶ Envoie de données multiples ne peut se faire qu'avec des chaines de caractères
2 | Solutions :
| ▶ Utilisation de ls d'exécutions ▶ Fonctions de conversion de liste de données chirées en chaines de caractères

# Algorithme RSA

1 | Algorithme de chirement asymétrique
2 | Se base sur deux conjectures : ▶ "casser" RSA par force brute nécessite de trouver la décomposition en facteurs premiers d'un nombre entier de grande taille ▶ les algorithmes existants ont une complexité exponentielle en la taille de la clé

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


# Protocole du modèle n°1

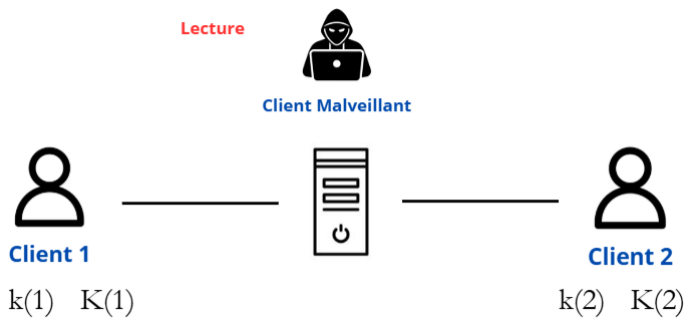
[picture p94: figure]

# Figure: Les clients échangent leur clé publique K respective

# Protocole du modèle n°1

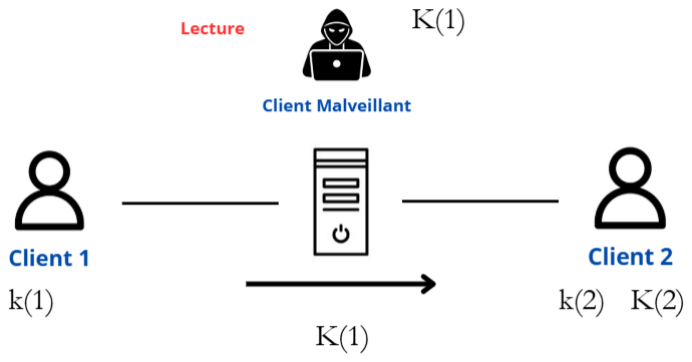
[picture p95: figure]

# Figure: Le client 1 envoie sa clé publique K(1) au client 2 en passant par le serveur

# Protocole du modèle n°1

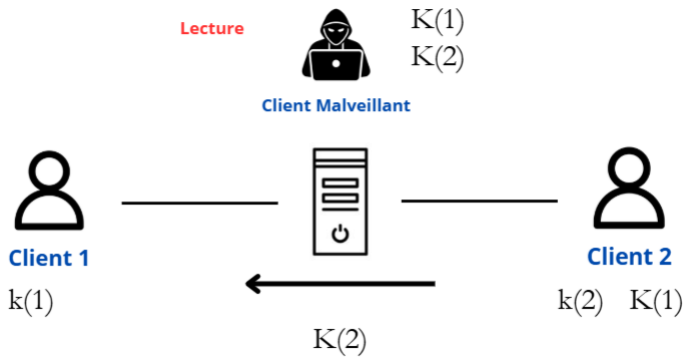
[picture p96: figure]

# Figure: Le client 2 envoie en retour sa clé publique K(2) au client 1 en passant par le serveur

# Protocole du modèle n°1


# Figure: Le client 1 chire le message m avec la clé K(2) et la fonction de chirement E

# Protocole du modèle n°1


# Figure: Le client 1 envoie le message chiré m′ au client 2 en passant par le serveur

# Protocole du modèle n°1

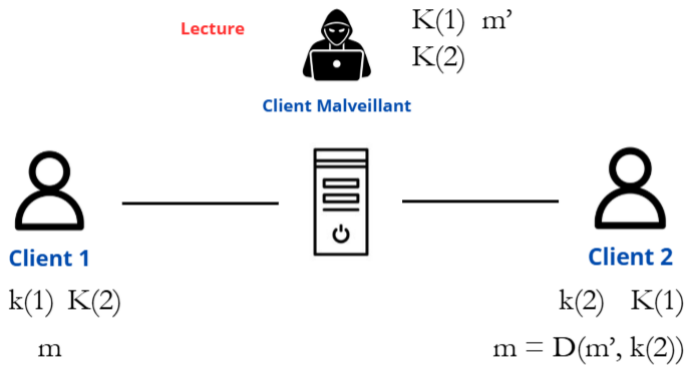
[picture p97: figure]

# Figure: Le client 2 reçoit m′ et le déchire avec sa clé privée k(2) et la fonction de déchirement D

# Test pratique

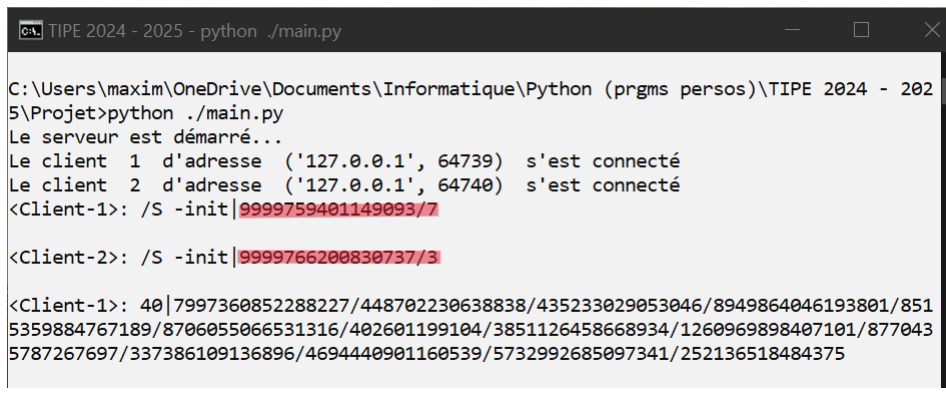
[picture p98: figure]

# Figure: Visuel du transit du message chiré 'Message secret ecrit par Maxime LE BLAN' par le serveur, et de ce que peut voir le client malveillant

# Test pratique

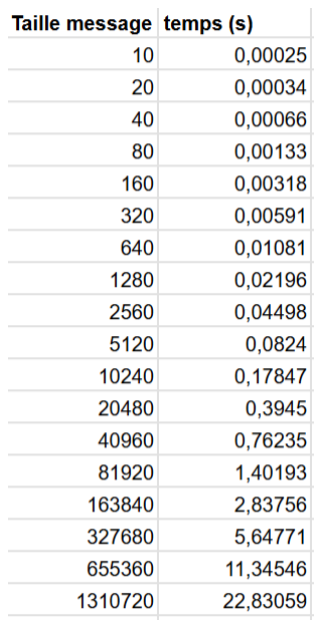
[picture p99: figure]

# Figure: Temps écoulé entre l'envoi et la réception d'un message en fonction de la taille de celui-ci avec RSA

# Ecacité de l'algorithme RSA


Remarque | : | La

# complexité temporelle de l'algorithme RSA est en O(m) avec m l'équivalent entier du message littéral

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

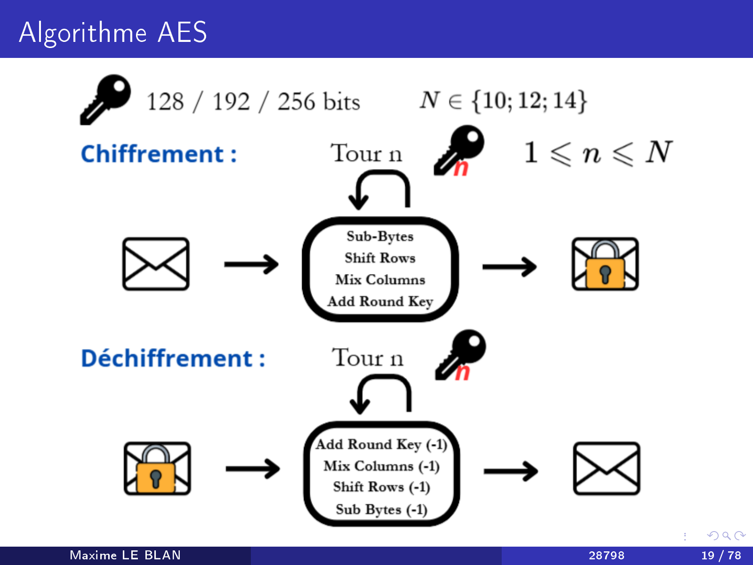
[picture p100: page 19]

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

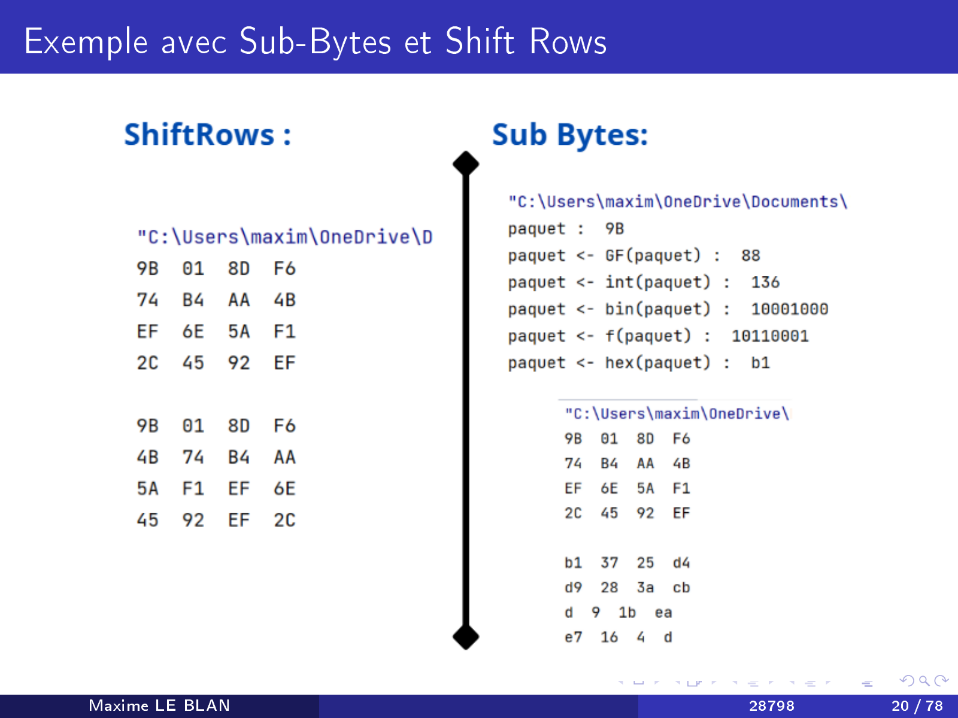
[picture p101: page 20]

# Protocole du modèle n°2

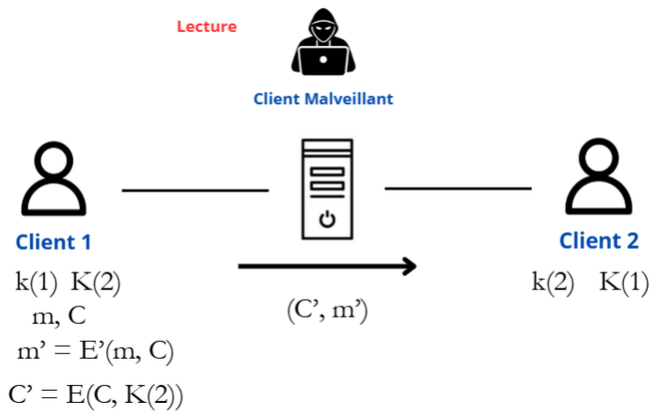
[picture p102: figure]

# Figure: Cette fois-ci, m est chiré avec la clé C de AES puis C est chirée avec

K(2)

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

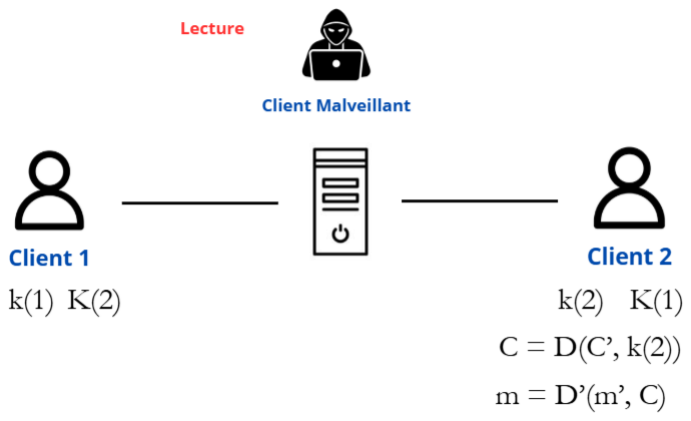
[picture p103: figure]

# Test pratique

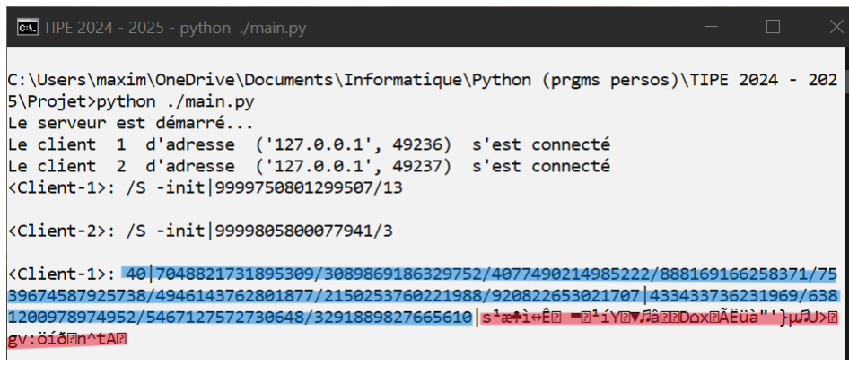
[picture p104: figure]

# Figure: Visuel du transit du message chiré 'Message secret ecrit par Maxime LE BLAN' par le serveur, et de ce que peut voir le client malveillant

# Test pratique


# Figure: Temps écoulé entre l'envoi et la réception d'un message en fonction de la taille de celui-ci

# Ecacité de l'algorithme AES


Remarque | : | La

# complexité temporelle de l'algorithme AES est en O(m) avec m l'équivalent entier du message littéral, mais AES reste en pratique plus ecace que RSA

# Problème de l'Homme du milieux

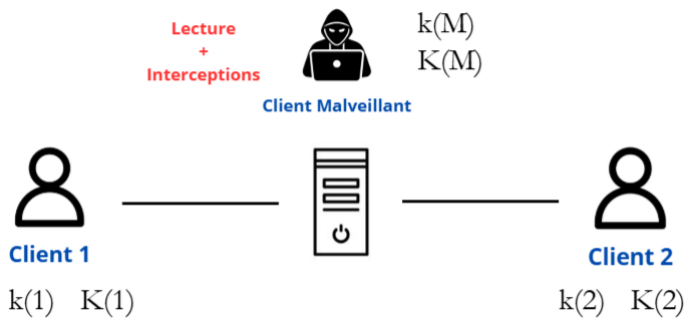
[picture p105: figure]

# Figure: Le client malveillant crée ses propres clés k(M) et K(M)

# Problème de l'Homme du milieux

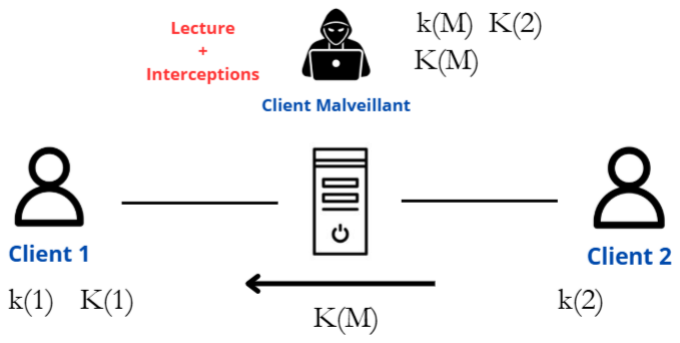
[picture p106: figure]

# Figure: Puis il échange K(2) avec K(M) lors de l'envoi de K(2)

# Problème de l'Homme du milieux

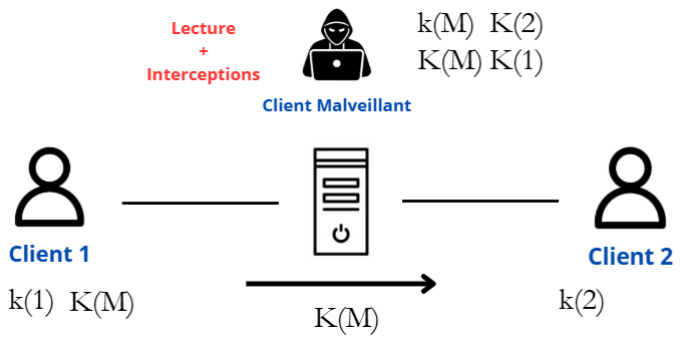
[picture p107: figure]

# Figure: Et il échange K(1) avec K(M) lors de l'envoi de K(1)

# Problème de l'Homme du milieux

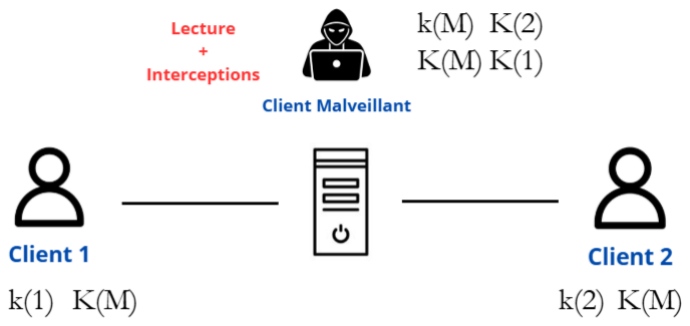
[picture p108: figure]

# Figure: Le client malveillant peut donc lire tous les messages échangés

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

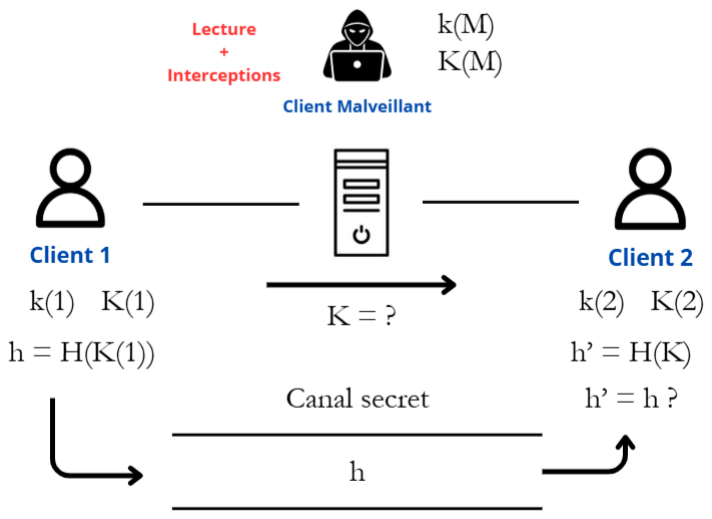
[picture p109: figure]

# Test pratique

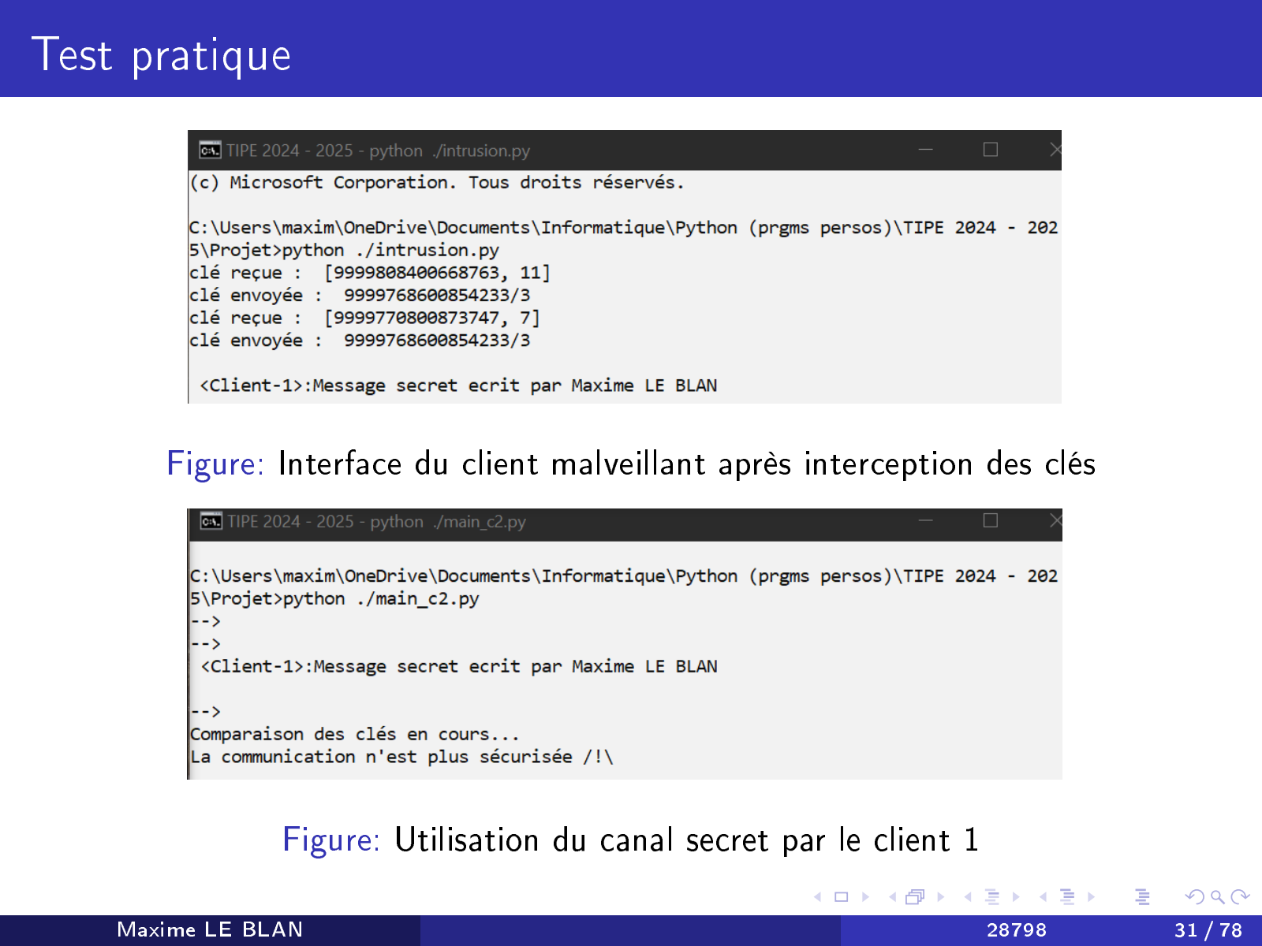
[picture p110: page 31]

# Figure: Interface du client malveillant après interception des clés

# Figure: Utilisation du canal secret par le client 1

# Conclusion

# Implémentation parallèlisée d'un réseau

# Implémentation d'un modèle ecace résistant à la lecture intrusive des données

# Problèmes :

# Implémentation du canal secret peu sécurisée et très simpliée

# L'intrusion du client malveillant dans la communication bloque tout échange sécurisé de données

# Pistes de réexion :

# Chercher une alternative au protocole SAS : utilisation de certicats pour l'authentication

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

# Annexe - Preuve déchirement RSA

# Par conséquent :

- Si m n'est pas un multiple de p, d'après le Petit théorème de Fermat,

# mp−1 ≡ 1 (mod p)

### ⇒ med ≡ m¹⁺k(p−1)(q−1) ≡ m × (mp−1

)

k(q−1)

# (mod p) ⇒ med ≡ m (mod p) - Si m est un multiple de p, alors med ≡ 0 (mod p) ⇒ med ≡ m (mod p)

# Donc med ≡ m (mod p) et de même, med ≡ m (mod q)

# p et q étant premiers, on a donc :

# med − m ≡ 0 (mod pq) ⇒ med ≡ m (mod n)

⇒ c

# d ≡ m (mod n)

# Annexe - Fonction de hachage idéale

# Propriétés :

# déterministe

# fonction de hachage avec une complexité amortie en O(1)

# résistance à la préimage : impossibilité, pour une valeur de hachage donnée, de construire un message ayant cette valeur

# résistance à la seconde préimage : impossibilité de trouver un second message ayant la même valeur de hachage qu'un message donné

# résistance aux collisions

# modier légèrement un message modie considérablement la valeur de hachage

# Annexe - Modules utilisés

# Imoportation de modules auxiliaires de Python import random as rd

import time
import threading
import socket
import sys
# Module utilis é pour l' utilisation d'une fonction de hachage

import hashlib
# Modules né cessaires pour l'impl é mentation d'AES avec des biblioth è ques from cryptography . hazmat . primitives . ciphers import Cipher , algorithms , modes from cryptography . hazmat . backends import default_backend

from cryptography . hazmat . primitives import padding
# Importation d'autres fichiers Python

import fonctions_utiles as fu
import algos_chiffrement as algos

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

# Annexe - algos_chirement.py

def creation_cles ( lst_nb_prem : list ):
""" Fonction prenant en param è tre une liste de nombres premiers et qui crée puis renvoie un couple de la forme
( cle_publique , cle_privee ) en suivant la mé thode de cré ation des clés de l' algorithme de chiffrement RSA \n
- cle_publique : tuple int \n
- cle_privee : int """
e = 2
# On choisit alé atoirement les valeurs de p et q distinctes p = lst_nb_prem . pop ( rd . randint (0 , len ( lst_nb_prem ) - 1) )

q = rd . choice ( lst_nb_prem )
# On choisit e et phi_n

n = p * q
phi_n = (p - 1) * (q - 1)

for i in range (2 , phi_n ): # on cherche le premier e qui convient en partant de e = 2
if fu . pgcd (i , phi_n ) == 1:
e = i
break
d = inverse_mod (e , phi_n )

return ((n , e) , d) # on renvoie (clé publique , clé priv ée)

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

# Annexe - algos_chirement.py

def dechiffrer_RSA_naif (x: int , cle_pv : int , n : int ) :
""" Fonction prenant en param è tre un entier x correspondant au message à dé chiffrer , cle_pv un entier
correspondant à la clé de dé chiffrement et n issue de la cle de chiffrement du message . Elle renvoie un entier
correspondant au message dé chiffr é """

reste = 1
for _ in range ( cle_pv ) :
reste *= x
reste = reste % n

return reste

def dechiffrer_RSA_v2 (x : int , cle_pv : int , n: int ):
""" Fonction prenant en param è tre un entier x correspondant au message à dé chiffrer , cle_pv un entier
correspondant à la clé de dé chiffrement et n issue de la cle de chiffrement du message . Elle renvoie un entier
correspondant au message dé chiffr é """

return modulo_exp (x , cle_pv , n)

# Annexe - algos_chirement.py

def chiffrer_chaine_RSA ( chaine :str , cle_pb :tuple , taille_facteur = -1) :
""" Fonction qui prend en param è tre une chaine de caract è res 'chaine ' et un tuple 'cle_pb ' et renvoie
une liste d'entiers correspondants aux facteurs de taille ' taille_facteur ', chiffr és avec la fonction ' chiffrer_RSA (...) ',
dont la concat é nation forme la chaine 'chaine ' avant son chiffrement """ if taille_facteur == ( -1) :
taille_facteur = len ( chaine )
chaine_chiffree = []
chaine_fractionnee = []
chaine_courante = ""

for i in range ( len ( chaine )): # On dé compose 'chaine ' en une liste de facteurs de taille ' taille_facteur '
chaine_courante += chaine [i ]
if len ( chaine_courante ) % taille_facteur == 0:
chaine_fractionnee . append ( chaine_courante ) chaine_courante = ""

if chaine_courante != "":
for i in range ( len ( chaine_courante ) , taille_facteur ): # on ajoute des espaces pour que le dernier facteur soit de taille taille_facteur chaine_courante += " "
chaine_fractionnee . append ( chaine_courante ) # on ajoute le dernier facteur de taille < ' taille_facteur ' ( sans compter les espaces )

for facteur in chaine_fractionnee : # On chiffre tous les facteurs avec la fonction ' chiffrer_RSA (...) '
int_facteur_courant = string_to_int ( facteur , base =95)
chaine_chiffree . append ( chiffrer_RSA_v2 ( int_facteur_courant , cle_pb )) return chaine_chiffree

# Annexe - algos_chirement.py

def dechiffrer_chaine_RSA ( liste :list , cle_pv : int , n: int , taille_entiers =1) : """ Fonction qui prend en param è tre une liste d'entiers 'liste ', un entier ' cle_pv ' et un entier n et
renvoie la concat é nation des chaines de caract ères dé chiffr ées avec ' dechiffrer_RSA (...) ' à partir des entiers
contenu dans 'liste ' repr é sentant des chaines de caract è res de taille ' taille_entiers ' """

chaine_dechiffree = ""

for i in range ( len ( liste ) ): # On dé chiffre tous les termes de liste sauf le dernier
chaine_courante = int_to_string ( dechiffrer_RSA_v2 ( liste [i ], cle_pv , n) , taille_entiers , b =95)
chaine_dechiffree += chaine_courante

return chaine_dechiffree

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

# Annexe - algos_chirement.py

def bytesub ( matrice : list [ list ]) :
""" Fonction bytesub qui prend en entr ée une matrice cod ée en hexad é cimal et renvoie le ré sultat
de la fonction aux_bytesub de AES appliqu ée à celle -ci """

return [[ aux_bytesub ( matrice [ i ][ j ]) for j in range ( len( matrice ))] for i in range ( len ( matrice ))]

def shiftrows ( matrice : list [ list ]) :
""" Fonction qui applique la fonction ShiftRows de AES sur la matrice """ n = len ( matrice )
matrice_finale = []
for d in range ( n):
matrice_finale . append ( fu . decale_liste ( matrice [d] , d ))

return matrice_finale

# Annexe - algos_chirement.py

# Algorithme AES impl é ment é avec une biblioth è que

def chiffrer_AES ( message :str , cle : bytes , vecteur : bytes ):
""" Fonction qui prend en param è tre un message , une clé et un vecteur et renvoie une chaine de
caract ère correspondant au chiffrement de 'message ' avec l'algorithme AES en utilisant la clé 'cle '
et le vecteur d' initialisation 'vecteur '\n
- message : chaine de caract è res\n
- cle : chaine de caract è res sur 32 octets \n
- vecteur : chaine de caract è res sur 16 octets """

padder = padding . PKCS7 (128) . padder ()
padded_data = padder . update ( message . encode ('utf -8 '))
padded_data += padder . finalize ()

cipher = Cipher ( algorithms . AES ( cle ) , modes . CBC ( vecteur ) , backend = default_backend () )
encryptor = cipher . encryptor ()
message_chiffre = encryptor . update ( padded_data ) + encryptor . finalize ()

return message_chiffre

# Annexe - algos_chirement.py

def dechiffrer_AES ( message_chiffre , cle : bytes , vecteur : bytes ):
""" Fonction qui prend en param è tre un message , une clé et un vecteur et renvoie une chaine de
caract ère correspondant au dé chiffrement de ' message_chiffre ' avec l' algorithme AES en utilisant la clé 'cle '
et le vecteur d' initialisation 'vecteur '\n
- message_chiffre : chaine de caract è res \n
- cle : chaine de caract è res sur 32 octets \n
- vecteur : chaine de caract è res sur 16 octets """

decryptor = Cipher ( algorithms . AES ( cle ) , modes . CBC ( vecteur ) , backend = default_backend () ). decryptor ()
decrypted_data = decryptor . update ( message_chiffre ) + decryptor . finalize ()

unpadder = padding . PKCS7 (128) . unpadder ()
unpadded_data = unpadder . update ( decrypted_data )
unpadded_data += unpadder . finalize ()

return unpadded_data . decode ('utf -8 ')

# Annexe - serveur.py

class Serveur :
""" Classe permettant de simuler un serveur informatique simplifi é à l'aide du module socket """

def __init__ ( self , modele :int , port =6390) :
self . host = ""
self . port = port
self . socket = None
self . clients = []
self . threads = {}
self . id_client = 1
self . arret = False
self . modele = modele

def close ( self ) :
""" Fonction qui vé rifie si le serveur doit s'é teindre ou non """ while True :
if self . arret == True :
break

# Annexe - serveur.py

def connections ( self ):
""" Fonction qui gère les connexions au serveur d'é ventuels clients en temps réel """
while True :
client , ip = self . socket . accept ()
self . clients . append (( self . id_client , client , ip ))
# on lance un fil d'exé cution pour chaque nouveau client afin de pouvoir recevoir ses messages

# on choisit la bonne fonction de ré ception en fonction du mod èle utilis é

if self . modele != 3:
self . threads [ str ( self . id_client ) ] = threading . Thread ( target = self . reception , args =[ client , self . id_client ])
else :
self . threads [ str ( self . id_client ) ] = threading . Thread ( target = self . reception_cm , args =[ client , self . id_client ])
self . threads [ str ( self . id_client ) ]. start ()

print ("Le client ", self . id_client , " d'adresse ", ip , " s'est connect é ")
self . id_client += 1

def transfert ( self , expediteur :str , destinataire , message :str , separateur =":") : """ Fonction qui transfert un message entre 2 clients """
new_msg = "<Client -" + expediteur + ">" + separateur + message destinataire . send ( new_msg . encode ("utf -8") )

# Annexe - serveur.py

def reception ( self , client , id_client : int) :
""" Fonction qui ré ceptionne les requ ê tes des clients et qui les traite pour les mod è les 1 et 2"""
while True :
requete_client = client . recv (500)
requete_client = requete_client . decode ("utf -8")
print ("<Client -" + str ( id_client ) + " >:", requete_client ) print () # on passe une ligne pour aérer l'affichage
if requete_client == "/S -close ":
print (" CLOSE ")
self . arret = True
else : # on envoie le message au bon destinataire en fonction de l'exp é diteur
if id_client == 1:
self . transfert ( str ( id_client ) , self . clients [1][1] , requete_client , separateur ="|")
else :
self . transfert ( str ( id_client ) , self . clients [0][1] , requete_client , separateur ="|")

# Annexe - serveur.py

def reception_cm ( self , client , id_client : int ) :
""" Fonction qui ré ceptionne les requ ê tes des clients et qui les traite pour le modèle 3 """
while True :
requete_client = client . recv (500)
requete_client = requete_client . decode ("utf -8")
decomp_msg = fu . decomposition_chaine ( requete_client , separateur ="|") print ("<Client -" + str ( id_client ) + " >:", requete_client )
print () # on passe une ligne pour aérer l'affichage
if requete_client == "/S -close ":
print (" CLOSE ")
self . arret = True
elif "/S -check " in requete_client : if id_client == 1:
destinataire = 1
else :
destinataire = 0
self . transfert ( str ( id_client ) , self . clients [ destinataire ][1] , requete_client , separateur ="|")

# Annexe - serveur.py

elif "/S -init " in requete_client :
if len ( decomp_msg ) > 2: # si le client malveillant veut envoyer une clé altérée
# on l'envoie au bon destinataire

expediteur = decomp_msg [2]
destinataire = int ( decomp_msg [3]) - 1
# on supprime les infos concernant l'exp é diteur et le destinataire

decomp_msg . pop ()
decomp_msg . pop ()
requete_client = fu . compression_arg_str ( decomp_msg , separateur = "|")
self . transfert ( expediteur , self . clients [ destinataire ][1] , requete_client , separateur ="|")
else : # sinon c'est la clé d'origine d'un client normal
# on envoie donc sa clé au client malveillant

self . transfert ( str ( id_client ) , self . clients [2][1] , requete_client , separateur ="|")
elif id_client != 3: # si le serveur reç oit un message d'un client normal
# on l'envoit au client malveillant

self . transfert ( str ( id_client ) , self . clients [2][1] , requete_client , separateur ="|")
else :
# on l'envoie au bon destinataire

expediteur = decomp_msg [4]
destinataire = int ( decomp_msg [5]) - 1
# on supprime les infos concernant l'expé diteur et le destinataire decomp_msg . pop ()

decomp_msg . pop ()
requete_client = fu . compression_arg_str ( decomp_msg , separateur ="|") self . transfert ( expediteur , self . clients [ destinataire ][1] ,
Maxime LE BLAN | requete_client , separateur ="|") | 28798 | 53 / 78

# Annexe - serveur.py

def run ( self ):
""" Fonction qui dé marre et ferme le serveur """
# cré ation du socket pour "dé marrer " le serveur

self . socket = socket . socket ( socket . AF_INET , socket . SOCK_STREAM ) self . socket . bind (( self . host , self . port ))
print ("Le serveur est dé marr é ... ")

self . socket . listen (1) # on le met en mode ré cepteur

connections = threading . Thread ( target = self . connections , args =[]) connections . start ()

execution = threading . Thread ( target = self . close , args =[]) execution . start ()

execution . join ()

for client in self . clients : client [1]. close ()
self . socket . close ()

# Annexe - client.py

class Client_RSA :
""" Classe permettant de simuler un client pouvant se connecter à un serveur informatique simplifi é
à l'aide du module socket , qui base le chiffrement sur l'algorithme du RSA """

def __init__ ( self , id: int , liste_nb_premiers , host =" localhost ", port =6390) : self .id = id
self . host = host
self . port = port
self . socket = None
self . cle_pv_RSA = None
self . cle_pb_RSA = None
self . cles_pb_RSA_autres = {}
self . liste_nb_premiers = liste_nb_premiers
self . init_envoi = False # permet de savoir si self . initialisation_RSA () a d éjà été exé cut ée dans self . envoyer ()
15 | self . init_recu = False | # permet de savoir si self . initialisation_RSA () a d
éjà été exé cut ée dans self . reception ()
# messages envoy és de la forme : " Client_X : taille_msg : message_chiffre " # On renomme les indices que l'on utilise dans le code pour pouvoir les modifier plus facilement

# et pour plus de visibilit é

| self . i_client = 0 self . i_taille_msg = 1 self . i_msg_chiffre = 2

# Annexe - client.py

def initialisation_RSA ( self , message : str , separateur ="|") :
""" Fonction qui crée la clé priv ée et la clé publique du client pour l' algo de chiffrement RSA .
Elle est exé cut ée à l' initialisation de la connection avec le serveur et partage la clé publique du client
avec un autre client connect é au serveur avec lequel il veut communiquer ."" "

cles = algos . creation_cles ( self . liste_nb_premiers )
self . cle_pb_RSA = cles [0]
self . cle_pv_RSA = cles [1]
msg = fu . compression_arg_str ([ self . cle_pb_RSA [0] , self . cle_pb_RSA [1]]) msg = message + separateur + msg

return msg

def envoyer ( self , socket ) :
""" Fonction permettant d'envoyer un message à un client en passant par le serveur """
try :
while True :
msg = input (" -->")
if msg == "/S -init " and not self . init_envoi :
socket . send ( self . initialisation_RSA ( msg ) . encode ("utf -8")) self . init_envoi = True
elif msg == "/S -close ":
socket . send ( msg . encode ("utf -8"))

# Annexe - client.py

else :
try :
if self .id == 1: # on chiffre le message avec la clé publique du bon client
# msg_chiffre = algos . chiffrer_RSA ( algos . string_to_int ( msg), self . cles_pb_RSA_autres ["2"])

msg_chiffre = algos . chiffrer_chaine_RSA ( msg , self . cles_pb_RSA_autres ["2"], taille_facteur =3)
else :
# msg_chiffre = algos . chiffrer_RSA ( algos . string_to_int ( msg), self . cles_pb_RSA_autres ["1"])

msg_chiffre = algos . chiffrer_chaine_RSA ( msg , self . cles_pb_RSA_autres ["1"], taille_facteur =3)
# on transforme le message sous forme de liste en chaine de caract è res

msg_chiffre = fu . compression_arg_str ( msg_chiffre ) msg_envoye = str ( len ( msg ) ) + "|" + str ( msg_chiffre ) # on ajoute la longueur du message chiffr é au message envoy é
msg_envoye = msg_envoye . encode ("utf -8")
socket . send ( msg_envoye )
except AssertionError :
print (" Erreur lors de la tentative de chiffrement du message . Veuillez essayer à nouveau ")
except ConnectionResetError :
print ("Dé connexion du serveur ... ") sys . exit ()

# Annexe - client.py

def reception ( self , socket ):
""" Fonction qui ré ceptionne les messages reçus du serveur """ try:
while True :
requete_serveur = socket . recv (500)
requete_serveur = requete_serveur . decode ("utf -8")
# requete_serveur est de la forme : " Client_X : taille_msg : message_chiffre "

decomp_msg = fu . decomposition_chaine ( requete_serveur ) id_expediteur = fu . id_client ( requete_serveur )

if "/S -init " in decomp_msg and not self . init_recu : # si on a pas enregistr é les clés publiques de l'autre client , on le fait self . cles_pb_RSA_autres [ id_expediteur ] = fu . extraction_arg_str ( decomp_msg [ self . i_msg_chiffre ])
self . init_recu = True
if not self . init_envoi : # si on a pas é chang é notre clé publique , on le fait
socket . send ( self . initialisation_RSA ("/S -init "). encode ("utf -8") )
self . init_envoi = True

# Annexe - client.py

else :
taille_msg = int ( decomp_msg [ self . i_taille_msg ])
# on reconvertit le message chiffr é ( str ) en liste d'entiers pour pouvoir ensuite le dé chiffrer

msg_chiffre = fu . extraction_arg_str ( decomp_msg [ self . i_msg_chiffre ])
# on vé rifie qui est l'exp é diteur pour prendre sa clé publique correspondante

if id_expediteur == 1:
# msg_dechiffre = algos . dechiffrer_RSA ( int ( decomp_msg [2]) , self . cle_pv_RSA , self . cle_pb_RSA [0])

msg_dechiffre = algos . dechiffrer_chaine_RSA ( msg_chiffre , self . cle_pv_RSA , self . cle_pb_RSA [0] , taille_entiers =3) else :
msg_dechiffre = algos . dechiffrer_chaine_RSA ( msg_chiffre , self . cle_pv_RSA , self . cle_pb_RSA [0] , taille_entiers =3) print ("\n", decomp_msg [ self . i_client ] + ":" + msg_dechiffre ) print ("\n-- >", end ="")
except ConnectionResetError :
print (" Connexion interrompue \ nSi le terminal est en attente , appuyez sur Entr ée")
sys . exit ()

# Annexe - client.py

def connection ( self ) :
""" Fonction permettant de connecter le client à un serveur """ self . socket = socket . socket ( socket . AF_INET , socket . SOCK_STREAM ) self . socket . connect (( self . host , self . port ))
envoi = threading . Thread ( target = self . envoyer , args =[ self . socket ]) recep = threading . Thread ( target = self . reception , args =[ self . socket ]) envoi . start ()
recep . start ()

class Client_AES_RSA ( Client_RSA ):
""" Classe fille de Client_RSA permettant de simuler un client pouvant se connecter à un serveur informatique simplifi é
à l'aide du module socket , qui base le chiffrement sur une combinaison de l' algorithme RSA et AES """
def __init__ ( self , id: int , liste_nb_premiers ):
Client_RSA . __init__ ( self , id , liste_nb_premiers )
# messages envoy és de la forme : " Client_X | taille_msg | cle_AES | vect_AES |

message_chiffre "
# On renomme les indices que l'on utilise dans le code pour pouvoir les modifier plus facilement

# et pour plus de visibilit é

self . i_client = 0
self . i_taille_msg = 1
self . i_cle_AES = 2
self . i_vect_AES = 3
self . i_msg_chiffre = 4

# Annexe - client.py

def envoyer ( self , socket ) :
""" Fonction permettant d'envoyer un message à un client en passant par le serveur """
try:
while True :
msg = input (" -->")
if msg == "/S -init " and not self . init_envoi :
# on envoie notre clé publique à l'autre client

socket . send ( self . initialisation_RSA ( msg , separateur ="|"). encode ("utf -8") )
self . init_envoi = True
elif msg == "/S -close ":
socket . send ( msg . encode ("utf -8"))
elif msg == "/S -check ":
# on construit le hash de la clé publique de l'exp é diteur et on l'envoie à l'autre client

cle_pb = str ( self . cle_pb_RSA [0]) + "/" + str ( self . cle_pb_RSA [1])
hash_cle = hashlib . sha256 ( cle_pb . encode () )
hash_cle = hash_cle . hexdigest ()
msg += "|" + hash_cle
socket . send ( msg . encode () )
else :
try :
cle_AES = fu . generateur_alea_chaine (32)
vecteur_AES = fu . generateur_alea_chaine (16)
# si on veut envoyer un msg au client 1, on chiffre avec la clé publique du client 2

24 | if self .id == 1: | # on chiffre le message avec la clé
publique du bon client
destinataire = "2"

# Annexe - client.py

else : # sinon c'est l'inverse
destinataire = "1"
# On chiffre le message avec la cle et le vecteur AES msg_chiffre = algos . chiffrer_AES ( msg , fu . encode_ascii ( cle_AES ) , fu . encode_ascii ( vecteur_AES )) msg_chiffre = msg_chiffre . decode ("latin -1")

# On chiffre la cle et le vecteur pour AES avec le RSA cle_AES = algos . chiffrer_chaine_RSA ( cle_AES , self . cles_pb_RSA_autres [ destinataire ], taille_facteur =4) vecteur_AES = algos . chiffrer_chaine_RSA ( vecteur_AES , self . cles_pb_RSA_autres [ destinataire ], taille_facteur =4) # on transforme le message , la clé et le vecteur sous forme de liste en chaine de caract è res

msg_chiffre = fu . compression_arg_str ([ msg_chiffre ]) cle_AES = fu . compression_arg_str ( cle_AES )
vecteur_AES = fu . compression_arg_str ( vecteur_AES )
# On construit le message que l'on va envoyer contenant toutes les infos né cessaires pour le destinataire msg_envoye = str ( len ( msg ) ) + "|" + cle_AES + "|" + vecteur_AES + "|" + msg_chiffre

msg_envoye = msg_envoye . encode ("utf -8")
socket . send ( msg_envoye )
except AssertionError :
print (" Erreur lors de la tentative de chiffrement du message . Veuillez essayer à nouveau ")
except ConnectionResetError :
print ("Dé connexion du serveur ... ") sys . exit ()

# Annexe - client.py

1 | def reception ( self , socket ):
2 | """ Fonction qui ré ceptionne les messages reçus du serveur """
3 | try:
4 | while True :
5 | requete_serveur = socket . recv (500)
6 | requete_serveur = requete_serveur . decode ("utf -8")
7 | decomp_msg = fu . decomposition_chaine ( requete_serveur , separateur ="|
")
8 | id_expediteur = fu . id_client ( requete_serveur )
9 | if "/S -init " in decomp_msg and not self . init_recu : | # si on a pas
enregistr é les clés publiques de l'autre client , on le fait
10 | self . cles_pb_RSA_autres [ id_expediteur ] = fu . extraction_arg_str (
decomp_msg [2])
11 | self . init_recu = True
12 | if not self . init_envoi : | # si on a pas é chang é notre clé
publique , on le fait
13 | socket . send ( self . initialisation_RSA ("/S -init ", separateur =
"|"). encode ("utf -8"))
14 | self . init_envoi = True
15 | elif "/S -check " in requete_serveur :
16 | print ("\ nComparaison des clés en cours ... ")
17 | # on construit le hash de la clé de l'autre client à partir de
notre base de donn ée
18 | cle_pb = str ( self . cles_pb_RSA_autres [ id_expediteur ][0]) + "/" +
str ( self . cles_pb_RSA_autres [ id_expediteur ][1])
19 | hash_cle = hashlib . sha256 ( cle_pb . encode () )
20 | hash_cle = hash_cle . hexdigest ()
21 | # on récup ère le hash envoy é par l'autre client
22 | hash_autre_cle = decomp_msg [ -1]

# Annexe - client.py

if hash_autre_cle != hash_cle :
print ("La communication n'est plus sé curis ée /!\ ") else :
print ("La communication est sé curis ée")
else :
# On extrait et dé chiffre la clé et le vecteur AES

cle_AES = fu . extraction_arg_str ( decomp_msg [ self . i_cle_AES ]) cle_AES = algos . dechiffrer_chaine_RSA ( cle_AES , self . cle_pv_RSA , self . cle_pb_RSA [0] , taille_entiers =4)
vecteur_AES = fu . extraction_arg_str ( decomp_msg [ self . i_vect_AES ])
vecteur_AES = algos . dechiffrer_chaine_RSA ( vecteur_AES , self . cle_pv_RSA , self . cle_pb_RSA [0] , taille_entiers =4)

# on récup ère le message chiffr é et on le dé chiffre msg_chiffre = decomp_msg [ self . i_msg_chiffre ]

msg_chiffre = msg_chiffre . encode ("latin -1")
msg_dechiffre = algos . dechiffrer_AES ( msg_chiffre , fu . encode_ascii ( cle_AES ) , fu . encode_ascii ( vecteur_AES )) print ("\n", decomp_msg [ self . i_client ] + ":" + msg_dechiffre ) print ("\n-- >", end ="")
except ConnectionResetError :
print (" Connexion interrompue \ nSi le terminal est en attente , appuyez sur Entr ée")
sys . exit ()

# Annexe - client.py

class ClientMalveillant ( Client_AES_RSA ):
""" Classe fille de la classe Client_AES_RSA qui initialise le client malveillant voulant lire des conversations
sé curis ées entre les autres clients connect és au même serveur , dans le cadre du mod èle n 3 avec la fonction
de hachage et le canal secret """
def __init__ ( self , id: int , liste_nb_premiers ):
Client_AES_RSA . __init__ ( self , id , liste_nb_premiers )
# Compteur indiquant le nombre d'é changes de clés que le Client Malveillant a effectu é avec les autres clients

self . nb_cles_echangees = 0

def initialisation_RSA ( self , message : str , separateur ="|", expediteur ="", destinataire =""):
""" Fonction qui crée la clé priv ée et la clé publique du client pour l' algo de chiffrement RSA .
Elle est exé cut ée à l' initialisation de la connection avec le serveur et partage la clé publique du client
avec un autre client connect é au serveur avec lequel il veut communiquer ."" "
if self . cle_pv_RSA == None : # si on a pas encore créé nos clés, on le fait cles = algos . creation_cles ( self . liste_nb_premiers )
self . cle_pb_RSA = cles [0]
self . cle_pv_RSA = cles [1]
msg = fu . compression_arg_str ([ self . cle_pb_RSA [0] , self . cle_pb_RSA [1]]) print ("clé envoy ée : ", msg )
msg = fu . compression_arg_str ([ msg , expediteur , destinataire ] , separateur ="| ")
msg = message + separateur + msg
return msg

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

# Annexe - client.py

1 | else :
2 | # On extrait et dé chiffre la clé et le vecteur AES
3 | cle_AES = fu . extraction_arg_str ( decomp_msg [ self . i_cle_AES ])
4 | cle_AES = algos . dechiffrer_chaine_RSA ( cle_AES , self . cle_pv_RSA ,
self . cle_pb_RSA [0] , taille_entiers =4)
5 | vecteur_AES = fu . extraction_arg_str ( decomp_msg [ self . i_vect_AES
])
6 | vecteur_AES = algos . dechiffrer_chaine_RSA ( vecteur_AES , self .
cle_pv_RSA , self . cle_pb_RSA [0] , taille_entiers =4) 7
8 | # on récup ère le message chiffr é et on le dé chiffre
9 | msg_chiffre = decomp_msg [ self . i_msg_chiffre ]
10 | msg_chiffre = msg_chiffre . encode ("latin -1")
11 | msg_dechiffre = algos . dechiffrer_AES ( msg_chiffre , fu .
encode_ascii ( cle_AES ) , fu . encode_ascii ( vecteur_AES ))
12 | print ("\n", decomp_msg [ self . i_client ] + ":" + msg_dechiffre )
13
14 | # on renvoie le message au destinataire chiffr é avec la clé
publique du destinataire
15 | # si on veut envoyer un msg au client 1 , on chiffre avec la clé
publique du client 2
16 | if id_expediteur == "1": | # on chiffre le message avec la clé
publique du bon client
17 | destinataire = "2"
18 | else : | # sinon c'est l'inverse
19 | destinataire = "1"

# Annexe - client.py

# On chiffre le message avec la cle et le vecteur AES msg_chiffre = algos . chiffrer_AES ( msg_dechiffre , fu . encode_ascii ( cle_AES ) , fu . encode_ascii ( vecteur_AES ) )

msg_chiffre = msg_chiffre . decode ("latin -1")
# On chiffre la cle et le vecteur pour AES avec le RSA

cle_AES = algos . chiffrer_chaine_RSA ( cle_AES , self . cles_pb_RSA_autres [ destinataire ], taille_facteur =4) vecteur_AES = algos . chiffrer_chaine_RSA ( vecteur_AES , self . cles_pb_RSA_autres [ destinataire ], taille_facteur =4)
# on transforme le message , la clé et le vecteur sous forme de liste en chaine de caract è res

msg_chiffre = fu . compression_arg_str ([ msg_chiffre ])
cle_AES = fu . compression_arg_str ( cle_AES )
vecteur_AES = fu . compression_arg_str ( vecteur_AES )
# On construit le message que l'on va envoyer contenant toutes les infos né cessaires pour le destinataire

msg_envoye = str( len ( msg_dechiffre )) + "|" + cle_AES + "|" + vecteur_AES + "|" + msg_chiffre + "|" + id_expediteur + "| " + destinataire
msg_envoye = msg_envoye . encode ("utf -8")
socket . send ( msg_envoye )
except ConnectionResetError :
print (" Connexion interrompue \ nSi le terminal est en attente , appuyez sur Entr ée")
sys . exit ()

def connection ( self ):
""" Fonction permettant de connecter le client à un serveur """ self . socket = socket . socket ( socket . AF_INET , socket . SOCK_STREAM ) self . socket . connect (( self . host , self . port ))
recep = threading . Thread ( target = self . reception , args =[ self . socket ]) recep . start ()

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

# Annexe - fonctions_utiles.py

def compression_arg_str ( liste_args : list , separateur ="/"):
""" Fonction qui prend en param è tre une liste d'objets pouvant ê tre convertis en chaine de caract ères , un sé parateur '/ ' et renvoie une chaine de caract è res contenant n param è tres et qui est de la forme 'arg [1]/ arg [2]/.../ arg [ n] ' """
arguments = ""
for i in range ( len ( liste_args )):
if i != len ( liste_args ) - 1:
arguments += str ( liste_args [i ]) + separateur else :
arguments += str ( liste_args [i ])
return arguments

def extraction_arg_str ( chaine_args : str , separateur ="/"):
""" Fonction qui prend en param è tre une chaine de caract è res contenant n arguments et de la forme 'arg [1]/ arg [2]/.../ arg [n]' , un sé parateur '/' et renvoie une liste contenant les n arguments de type int """
chiffres = " 0123456789 "
liste_args = []
arg_courant = ""
for i in range ( len ( chaine_args )) :
if chaine_args [i] != separateur and chaine_args [i] in chiffres : arg_courant += chaine_args [i]
else :
liste_args . append ( int ( arg_courant ))
arg_courant = ""
if arg_courant != "":
liste_args . append (int ( arg_courant ) ) return liste_args

# Annexe - fonctions_utiles.py

def decomposition_chaine ( chaine : str , separateur ="|") :
""" Fonction qui prend en param è tre une cha îne de caract è res que l'on peut diviser en sous - cha î nes sé par ées par un sé parateur ':' et renvoie une liste contenant ces sous - cha î nes """
liste_sous_chaines = []
arg_courant = ""
for i in range ( len ( chaine )):
if chaine [ i] != separateur :
arg_courant += chaine [ i]
else :
liste_sous_chaines . append ( arg_courant ) arg_courant = ""
if arg_courant != "":
liste_sous_chaines . append ( arg_courant ) return liste_sous_chaines

def id_client ( chaine : str ) :
""" Fonction qui prend une chaine de caract è res de type '<Client - * > *** ' et renvoie l'entier * en chaine de caract ères """
chiffres = " 0123456789 "
id_passe = False
id = ""
for char in chaine :
if char in chiffres :
id_passe = True
id += char
elif id_passe :
break
return id

# Annexe - fonctions_utiles.py

def importer_fichier ( nom_fichier :str , type ="int "):
""" Importe un fichier texte et ajoute chaque ligne du fichier dans une liste Python que la fonction renvoie """
liste_nb_premiers = []
with open ( nom_fichier , "r") as fichier :
contenu = fichier . readlines ()
for ligne in contenu :
ligne_actuelle = ligne . rstrip ("\n")
if type == " int ":
liste_nb_premiers . append ( int ( ligne_actuelle )) else :
liste_nb_premiers . append ( ligne_actuelle ) return liste_nb_premiers

def generateur_alea_chaine ( taille_chaine :int ):
""" Fonction qui génère alé atoirement une chaine de caract è res de taille ' taille_chaine ', compos ée des lettres de l'alphabet en minuscule , et la renvoie """
liste_int_a_char = " abcdefghijklmnopqrstuvwxyz "
nb_char = len ( liste_int_a_char )
chaine_alea = ""
for _ in range ( taille_chaine ):
i = rd . randint (0 , nb_char - 1) chaine_alea += liste_int_a_char [i] return chaine_alea

# Annexe - fonctions_utiles.py

def concat_chaine ( chaine :str , n: int ) :
""" Fonction qui renvoie la concat é nation de 'chaine ' (n -1) fois """

chaine_finale = ""
for _ in range ( n):
chaine_finale += chaine

return chaine_finale

def encode_ascii ( chaine :str ):
""" Fonction qui transforme une chaine str en bstr (ie en code ASCII )\n
NB : elle fait la même chose que la fonction native bytes ( chaine , encoding =" ascii ") """

return bytes ( chaine , encoding ="utf -8")

# Annexe - fonctions_utiles.py

1 | def matrice_gf ( chaine : str , taille =16) :
2 | """ Renvoie la matrice GF sous forme de matrice de type list [ list ] """
3 | matrice_gf = decomposition_chaine ( chaine , separateur =" ")
4 | matrice_gf_bis = []
5 | matrice_gf_finale = []
6 | ligne_gf = []
7
8 | for i in range ( len ( matrice_gf )):
9 | if "\n" in matrice_gf [i ]:
10 | matrice_gf_bis . append ( matrice_gf [ i ][:( -1) ])
11 | elif matrice_gf [i ] != "":
12 | matrice_gf_bis . append ( matrice_gf [ i ])
13
14 | for i in range ( taille ) :
15 | for j in range ( taille ):
16 | ligne_gf . append ( matrice_gf_bis [i* taille + j ])
17 | if j == taille - 1:
18 | matrice_gf_finale . append ( ligne_gf )
19 | ligne_gf = []
20
21 | return matrice_gf_finale

# Annexe - fonctions_utiles.py

1 | def conversion_matrice ( matrice : list [ list ], fonction , base =10) :
2 | """ Fonction qui applique la fonction de conversion 'fonction ' sur chaque case
| de la matrice carr ée """
3 | res = matrice . copy ()
4 | for i in range ( len ( matrice )) :
5 | for j in range ( len ( matrice ) ):
6 | if base != 10:
7 | res [i ][ j ] = fonction ( res [ i ][ j], base )
8 | else :
9 | res [i ][ j ] = fonction ( res [ i ][ j ])
10
11 | return res

# Annexe - fonctions_utiles.py

def produit_matriciel ( m1 : list [ list [ int ]] , m2 : list [ list [int ]] , n1 =( -1 , -1) , n2 =( -1 , -1) ):
""" Fonction qui renvoie le produit matriciel des matrices m1 et m2 """ assert ( n1 [1] == n2 [0])
if n1 == ( -1 , -1) :
n = len ( m1 )
p = n
q = n
else :
n , p = n1 [0] , n1 [1]
q = n2 [1]
res = [[0 for _ in range ( q)] for _ in range ( n)] for i in range ( n):
for j in range (q) :
somme = 0
for k in range (p ):
somme += m1 [i ][ k] * m2 [k ][ j] res [i ][ j] = somme
return res

def somme_matricielle ( m1 : list [ list [ int ]] , m2 : list [ list [int ]] , n: int , p : int ) : """ Fonction qui renvoie la somme des matrices m1 et m2 """
res = [[0 for _ in range ( p)] for _ in range ( n)]
for i in range ( n):
for j in range (p) :
res [i ][ j] = m1 [i ][ j ] + m2 [ i ][ j]
return res

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

# Annexe - fonctions_utiles.py

def affiche_matrice ( m: list [ list ]) :
""" Fonction qui affiche une matrice carr ée """ for i in range ( len (m)) :
for j in range ( len (m )):
print ( m[i ][ j] , " ", end ="")
print ()

def decale_liste ( liste : list , d: int ):
""" Fonction qui dé cale les élé ments de la liste de 'd' vers la droite et renvoie le ré sultat """
liste_bis = liste . copy ()
liste_finale = []
d_bis = d

if d == 0:
return liste

while d_bis > 0:
liste_finale = []
liste_finale . append ( liste_bis . pop () ) for el in liste_bis :
liste_finale . append ( el )
liste_bis = liste_finale . copy () d_bis -= 1

return liste_finale
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
