maxime-leblan/Projet-E3-2026-ESIEE-Paris/Rapport/Rapport projet/Partie_commune/partiecommune.tex

\subsection{Remerciement}

\uline{\textbf{Institutions et Direction}}

Ce projet n'existerait pas sans l'ESIEE Paris, école d'ingénieurs française située à Noisy-le-Grand, membre fondateur de l'Université Gustave Eiffel et membre de la Chambre de Commerce et d'Industrie (CCI) Paris Île-de-France. Nous remercions sincèrement son directeur, Monsieur Jean Mairesse, pour les opportunités que nous offre cette école, notamment le Jour des Projets organisé chaque année.
Nos remerciements vont à Madame Christine Cévaër, responsable des événements Jour des Projets et Coaching Entrepreneuriat \& Innovation, ainsi que vice-présidente du jury. 
Nous remercions également Madame Luciana Castro-Goncalves, présidente du jury du Jour des Projets 2026, ainsi que tous les autres membres du jury 2026. 
Nous associons à ces remerciements les quatre partenaires du Jour des Projets 2026 : MEMSCAP, NXP, Weeroc et l'AA-ESIEE, pour avoir cru en cette journée et en faire une expérience des plus enrichissantes.

\bigskip

\uline{\textbf{Corps Enseignant et Support Technique}}

Nous tenons particulièrement à remercier Madame Ting Wang, enseignante-chercheuse à l'ESIEE Paris et tutrice de ce projet. Ses précieux conseils, sa rigueur scientifique et son accompagnement tout au long du projet ont été essentiels pour structurer notre démarche et répondre aux exigences des projets de fin d'année de première année de cycle ingénieur.
Nous remercions chaleureusement Monsieur Laurent Bues ainsi que Monsieur Carlos Pintos pour leur savoir-faire apporté lors de la réalisation des cartes électroniques.

\bigskip

\uline{\textbf{Partenaires Professionnels et Experts Métier}}

Enfin, ce projet n'aurait pu coller aussi fidèlement aux réalités du terrain sans l'implication de professionnels du secteur du bâtiment et des travaux publics (BTP).
Nous remercions vivement Monsieur Luc-Géry Helle, directeur régional génie civil de GTM OUEST chez VINCI Construction France, pour la richesse de nos échanges sur notre projet et le domaine du BTP. 
Toute notre gratitude va également à Monsieur Mathieu Baré, directeur prévention délégation génie civil Ouest chez VINCI Construction France, grâce à qui nous avons pu nous rendre sur le chantier de la gare de Nanterre La Folie sur la future ligne 15 du Grand Paris Express, ainsi que bénéficier de son expertise en matière de sécurité et de prévention au sujet de notre projet.

\subsection{Introduction}

\input{Introduction/introduction.tex}

\subsection{Specifications et Objectifs }

L'idée principale de notre projet, c'est d'éviter les collisions entre les engins de chantier et les ouvriers à pied. Pour y arriver, nous avons défini que notre système devait remplir plusieurs fonctions essentielles. La première, c'était d'être capable de détecter un ou plusieurs ouvriers autour du véhicule en temps réel. Il fallait surtout pouvoir calculer exactement où ils se trouvaient par rapport à une zone de sécurité virtuelle délimitée autour de l'engin.

Ensuite, si un ouvrier franchit cette zone de danger, le système doit impérativement alerter les deux parties de manière instantanée. Du côté de l'ouvrier, il nous fallait une alerte sonore et visuelle directement sur son boîtier pour qu'il s'éloigne au plus vite. Du côté du conducteur, il lui fallait un retour visuel dans sa cabine (via un écran) pour savoir exactement de quel côté se trouvait le danger, le tout avec à une alarme sonore pour attirer son attention.

Nous avons aussi dû prendre en compte les conditions de travail réelles. Sur un chantier, le matériel est mis à rude épreuve. Le système devait donc être robuste : il devait résister à la pluie, à la poussière, aux gravats et surtout aux vibrations de l'engin sans se déconnecter. 

\subsection{Mise en oeuvre du prototype}
\input{Partie_commune/setupmachine.tex}

\subsection{Résultats et analyse}
\input{Partie_commune/resultats.tex}

\subsection{Conclusion }

En dépit des contraintes de temps qui nous ont été imposées, notre équipe est parvenue à l'élaboration d'une solution permettant aux utilisateurs de notre système de configurer une zone de sécurité complètement personnalisable et modifiable avec une précision correcte mais qui nécessiterait cependant d’être affinée en cas de poursuite du projet. Comme mentionné dans ce rapport, de nouvelles fonctionnalités utilisant des capteurs et des technologies supplémentaires permettraient d’améliorer la robustesse et la précision de notre système. De plus, le choix technologique ayant été en partie influencé par la limitation de notre budget, nous sommes conscient que celle-ci ne répond pas parfaitement à toutes les exigences d’une application dans le secteur du BTP. Nous sommes néanmoins parvenus à en tirer des résultats prometteurs qui nous permettrait d’envisager une application dans un éventuel autre domaine ou bien à l’attention de plus petites entreprises qui pourraient être intéressées.
