maxime-leblan/Projet-E3-2026-ESIEE-Paris/Rapport/Rapport projet/Abstract/Abstract.tex

Actuellement, la mise en place d'un système visant à prévenir les collisions entre les engins et les piétons dans le secteur du BTP est une question sur laquelle un certains nombre d'entreprises ont tenté d'apporter une réponse. Dans le cadre de ce projet étudiant, nous proposons une solution basée sur la technologie UWB qui possède l'avantage d'être plutôt bien adaptée dans la plupart des environnements caractéristiques des sites de construction. Notre approche tente également de produire le prototype d'un système accessible financièrement parlant pour des petites entreprises, tout en gardant des options de personnalisation que toutes les solutions actuelles ne proposent pas à ce jours. De nombreuses améliorations restent cependant possible à mettre en oeuvre compte tenu de la courte phase d'élaboration de notre projet qui a été de sept semaines.
