maxime-leblan/Projet-E3-2026-ESIEE-Paris/Rapport/Rapport projet/Software/software_maxime.tex

% Ecriture de la partie Software du rapport

Afin d'être capable d'estimer avec précision la position du compagnon en temps réel tout en étant capable de retranscrire l'information le plus rapidement possible et de la manière la plus exacte, nous avons divisé le travail à effectuer sur la partie software en plusieurs parties :

\begin{itemize}
    \item L'implémentation d'un repère virtuel en trois dimensions permettant au hub de se représenter l'emplacement des ancres, des tags portés par les compagnons ainsi que la délimitation de la zone de sécurité de l'engin.
    \item La recherche puis l'implémentation d'algorithmes dont l'objectif est de situer précisément dans le repère du Hub la position des compagnons ainsi que la distance de chacun d'entre eux par rapport à l'engin de chantier.
    \item L'écriture d'un programme de retranscription visuel du repère virtuel du Hub sur l'écran du conducteur de l'engin de chantier afin de pouvoir visualiser toutes les informations collectées par le hub de la manière la plus concise et claire possible. Ce programme doit également permettre au conducteur de pouvoir personnaliser la zone de sécurité de l'engin quand il le souhaite, ce qui implique une interface utilisateur simple et épurée.
    \item L'implémentation des programmes permettant de faire communiquer les microcontrôleurs ESP32-S3 (ancres et tags) avec l'ESP32-WROVER-E (hub) ainsi que des programmes permettant de faire la liaison entre les librairies contenant les algorithmes de calcul mathématiques liés au repère en trois dimensions et le hub.
\end{itemize}
\bigskip % Pour sauter une ligne
Nous allons donc dans un premier temps nous intéresser à l'implémentation du repère en lui-même et du programme de visualisation du repère que nous avons utilisé pour vérifier le bon fonctionnement de nos différents algorithmes mathématiques de manipulation d'objets au sein d'espaces vectoriels.

Mais avant d'étudier ce premier aspect, voici un aperçu global du fonctionnement de l'algorithme de chaque sous-système de notre prototype dans la partie ci-dessous.
\newpage
\subsection{Organigrammes des sous-systèmes}

\begin{figure}[!ht]
\centering 
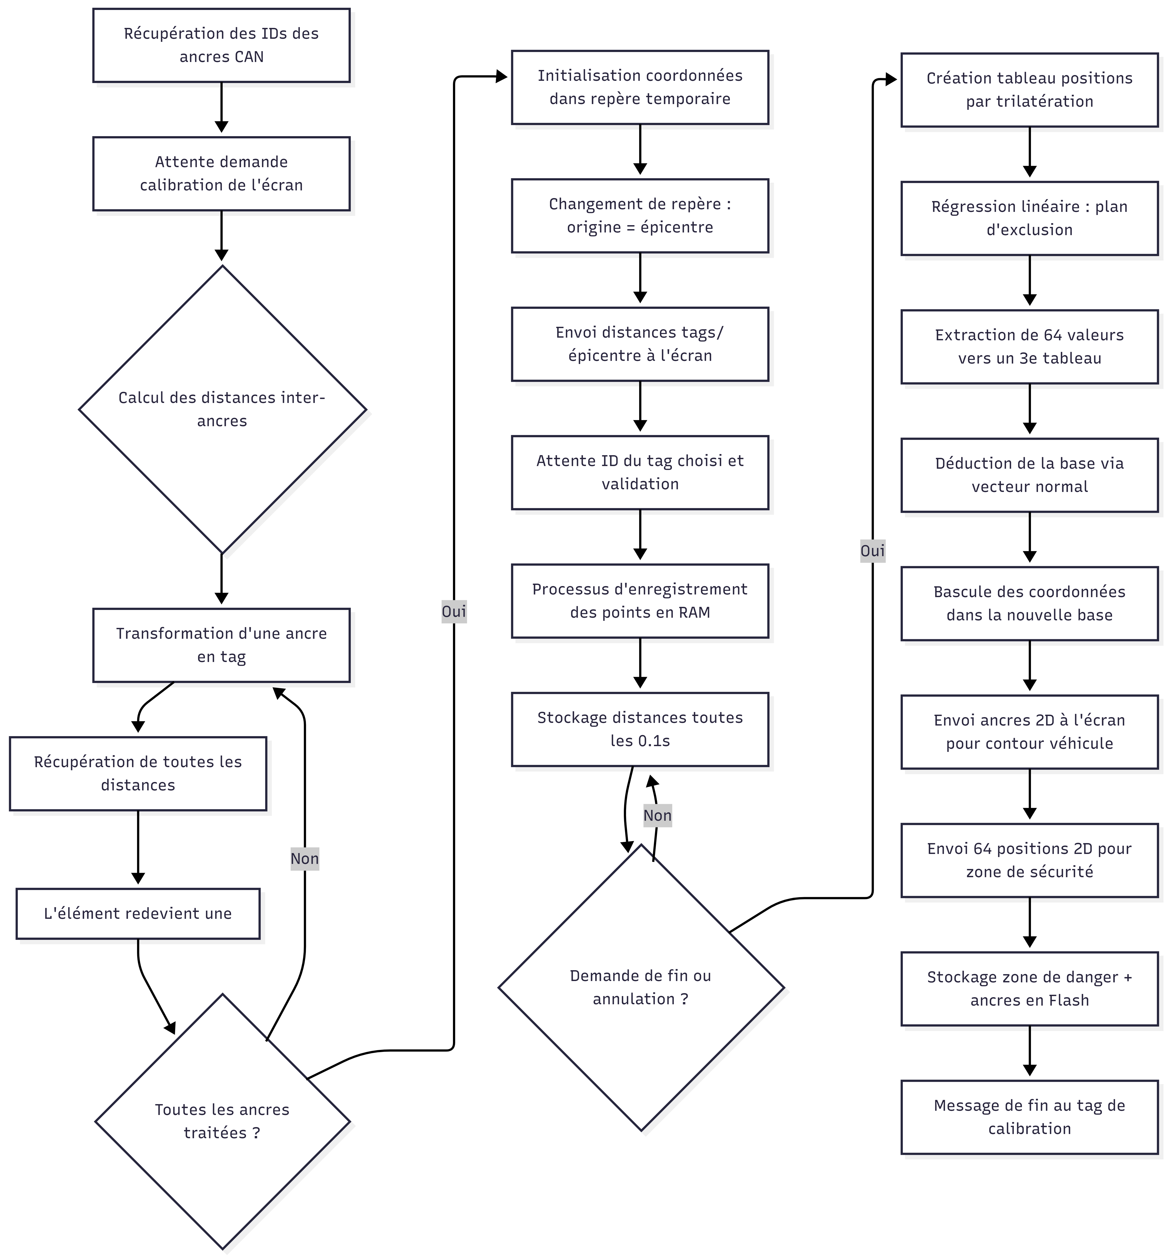
[picture p132: Rapport/Rapport projet/Figures/organigramme_hub_init.png]
 
\caption[Programme d'initialisation du hub]{Programme d'initialisation du hub}
\end{figure}

\newpage

\begin{figure}[!ht]
\centering 
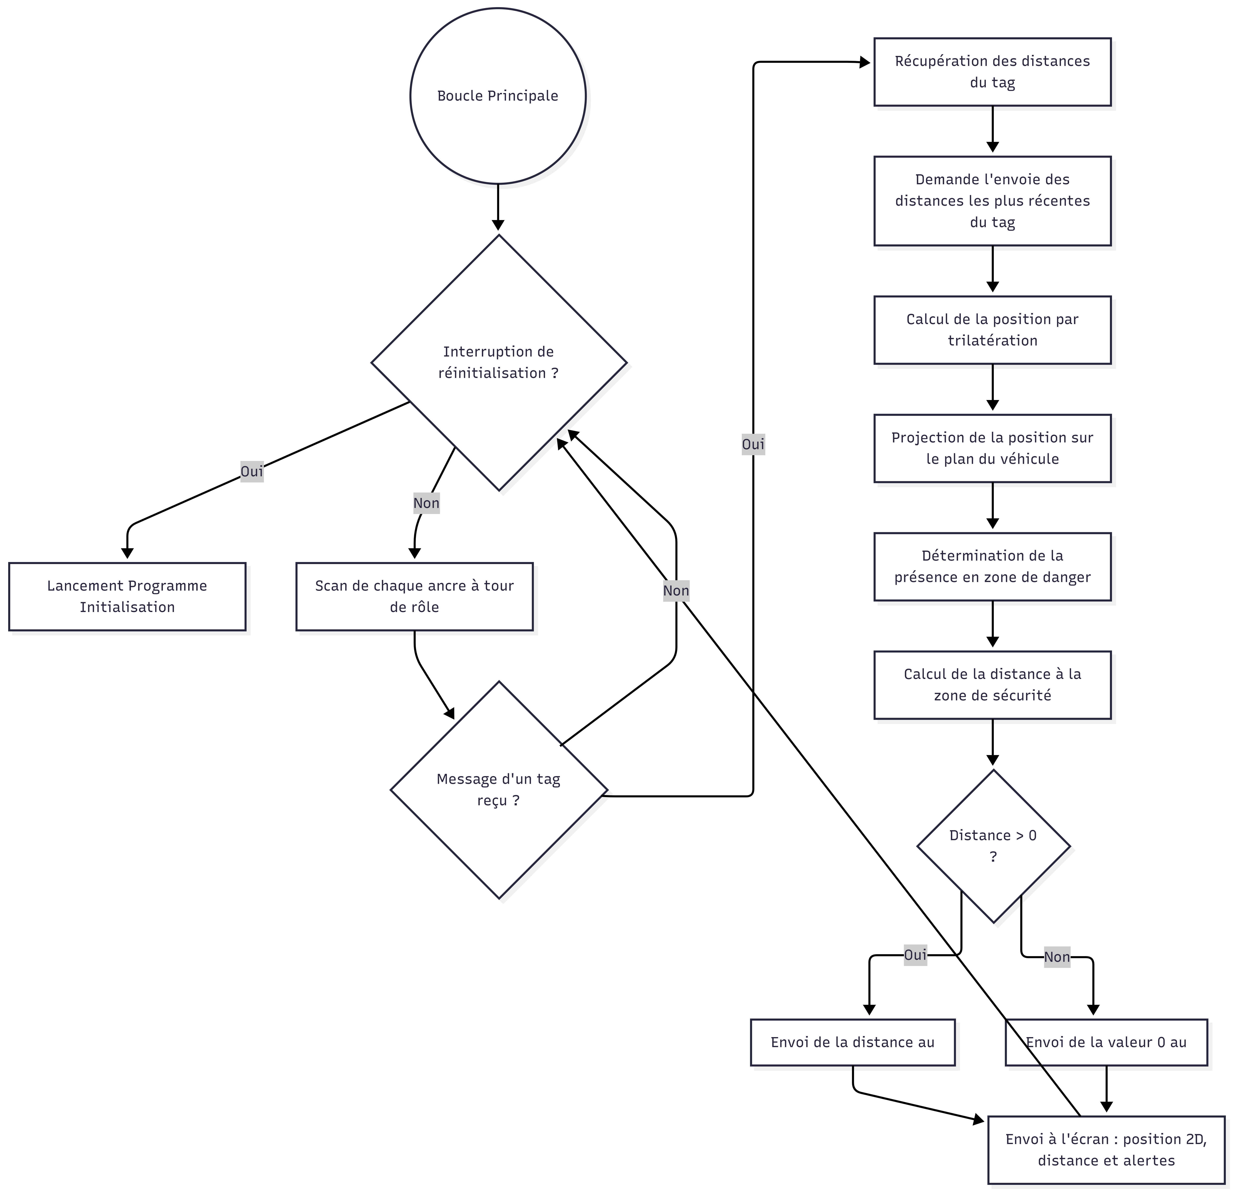
[picture p133: Rapport/Rapport projet/Figures/organigramme_hub_principal.png]
 
\caption[Programme principal du hub]{Programme principal du hub}
\end{figure}

\newpage

\begin{figure}[!ht]
\centering 
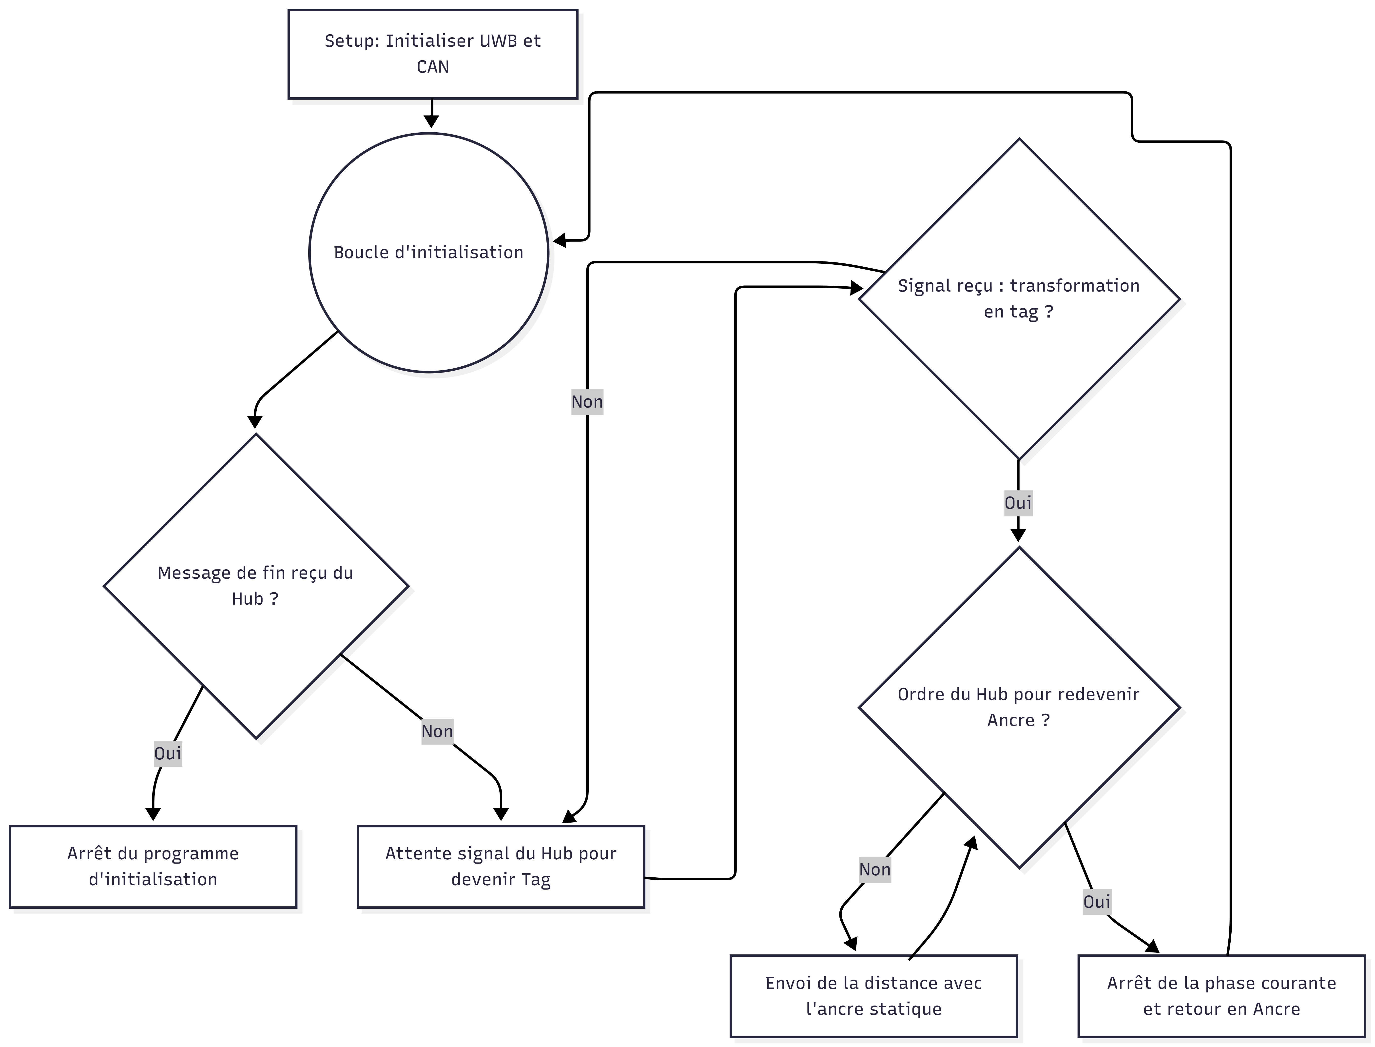
[picture p134: Rapport/Rapport projet/Figures/organigramme_ancre_init.png]
 
\caption[Programme d'initialisation d'une ancre]{Programme d'initialisation d'une ancre}
\end{figure}

\newpage

\begin{figure}[!ht]
\centering 
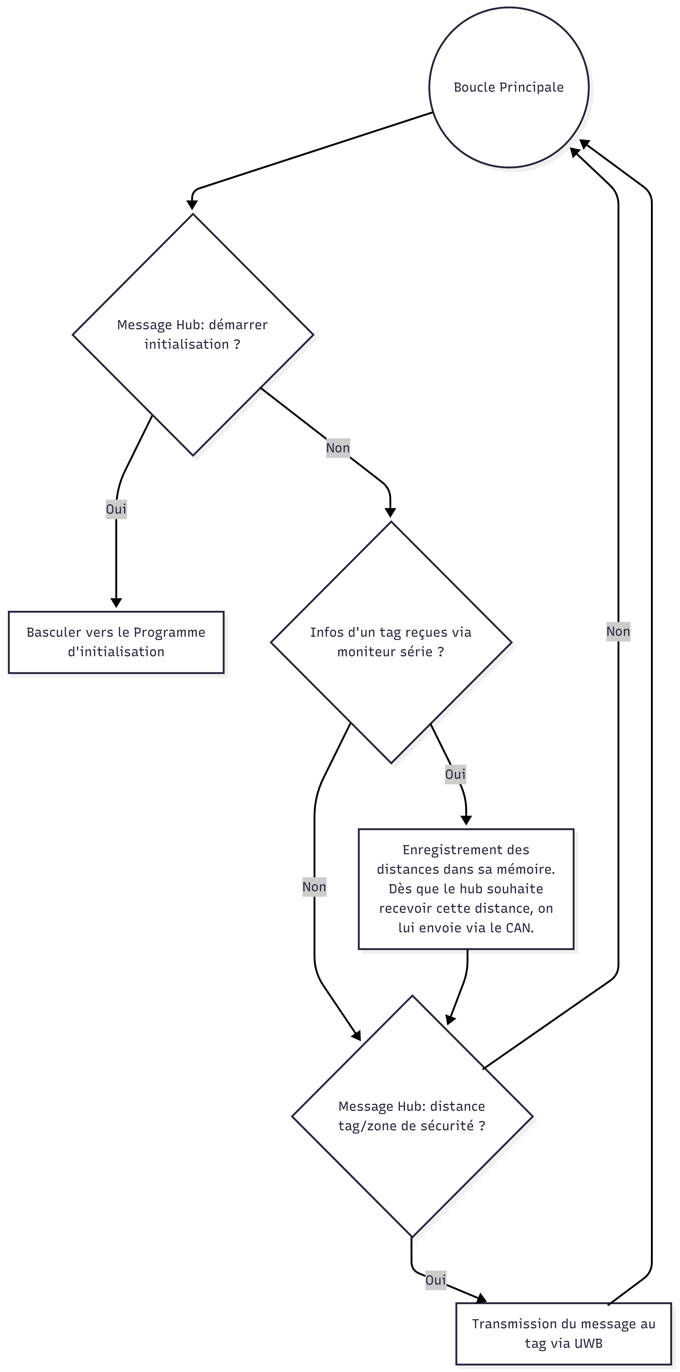
[picture p135: Rapport/Rapport projet/Figures/organigramme_ancre_principal.png]
 
\caption[Programme principal d'une ancre]{Programme principal d'une ancre}
\end{figure}

\newpage

\begin{figure}[!ht]
\centering 
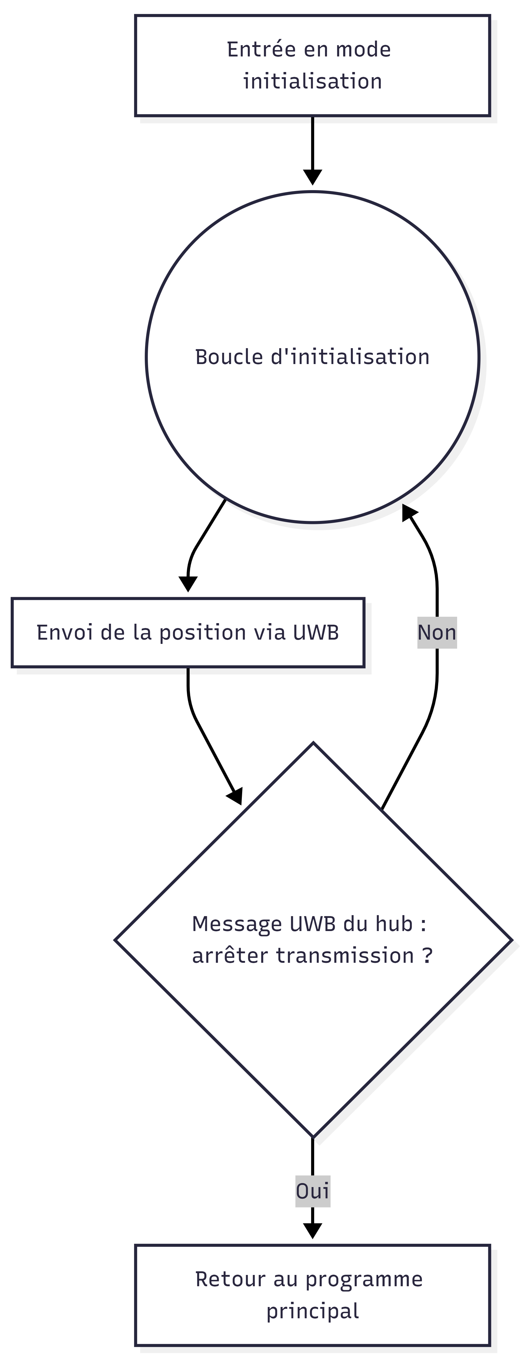
[picture p136: Rapport/Rapport projet/Figures/organigramme_tag_init.png]
 
\caption[Programme d'initialisation d'un tag]{Programme d'initialisation d'un tag}
\end{figure}

\newpage

\begin{figure}[!ht]
\centering 
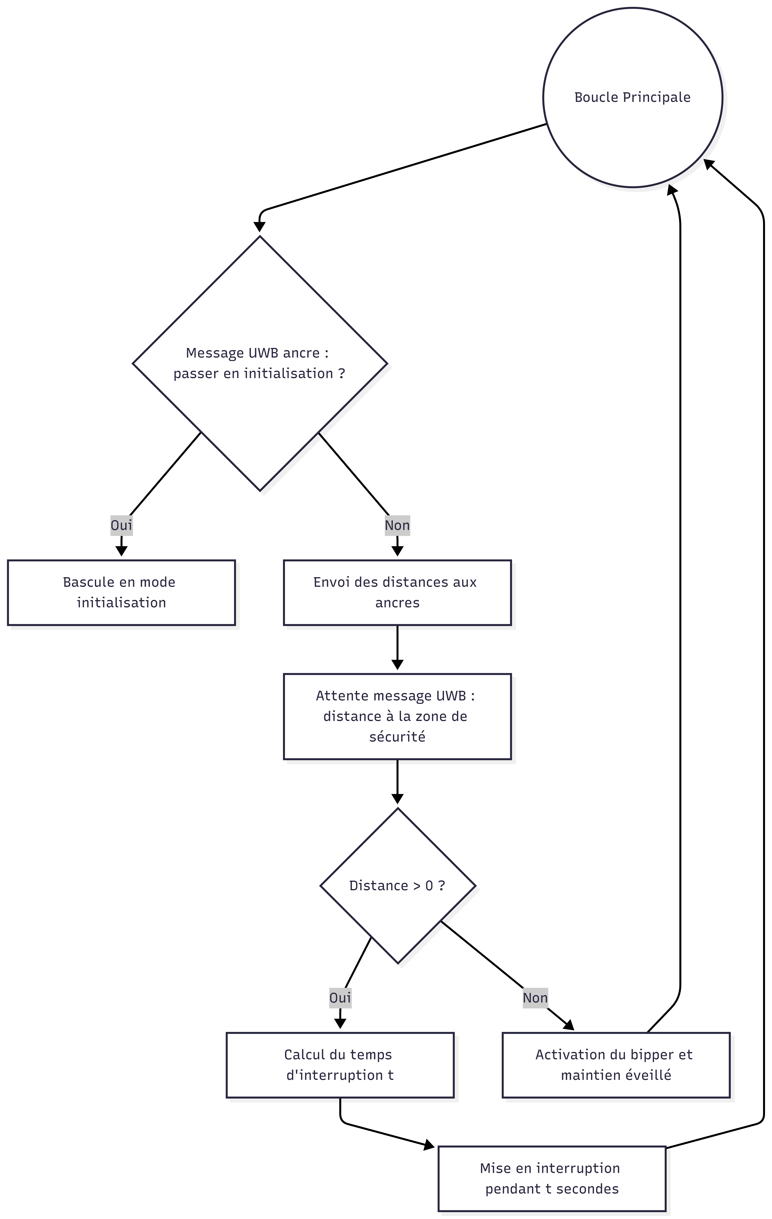
[picture p137: Rapport/Rapport projet/Figures/organigramme_tag_principal.png]
 
\caption[Programme principal d'un tag]{Programme principal d'un tag}
\end{figure}

\newpage

\subsection{Repère du Hub en trois dimensions}

L'objectif étant de déterminer de la manière la plus exacte possible la position d'un tag par rapport à notre engin de chantier, il faut donc que notre système utilise un repère auquel le hub pourrait se référer pour pouvoir positionner les ancres fixées sur le véhicule, les tags des compagnons ainsi que la zone de sécurité autour du véhicule.

Pour l'implémentation de ce dispositif, nous avons dans un premier temps rédigé une librairie allégée dénommée {\ttfamily{V3.h}} permettant de représenter des vecteurs en trois dimensions, puis nous avons utilisé le paradigme de la \uline{Programmation Orientée Objets (POO)} afin de modéliser les classes suivantes :

\begin{itemize}
    \item {\ttfamily{\textbf{UWBModule}}} : Cette classe permet de représenter à la fois les tags ainsi que les ancres en stockant comme information pour chaque module son identifiant et sa position.
    \item {\ttfamily{\textbf{UWBModuleList}}} : Cette classe stocke plusieurs module UWB dans une même structure de données, permettant ainsi d'effectuer des manipulations sur l'ensemble des ancres et des tags connus du hub. Afin de garantir un accès efficace aux données, la structure de données de dictionnaire native en {\ttfamily{C++ <unordered\_map.h>}} a été utilisée afin de garantir un accès aux données avec une complexité temporelle en {\emph{O(1)}}.
\end{itemize}
\bigskip
<Inclure un schéma représentant la structure des 2 classes>
\bigskip

Pour la librairie {\ttfamily{V3.h}}, nous avons uniquement implémenté les fonctions mathématiques de base dont nous avions besoin afin de limiter la place prise par la librairie sur la Flash des ESP32. Nous avons donc écris le code des fonctions suivantes :

\begin{itemize}
    \item {\ttfamily{\textbf{getNormalised()}}} : Renvoie le vecteur normalisé du vecteur sur lequel la méthode a été appelée.
    \item {\ttfamily{\textbf{prodScal(const V3 \& a, const V3 \& b)}}} : Renvoie le produit scalaire canonique en trois dimensions du vecteur {\ttfamily{a}} et le vecteur {\ttfamily{b}}.
    \item {\ttfamily{\textbf{prodScal2D(const V3 \& a, const V3 \& b)}}} : Renvoie le produit scalaire canonique en deux dimensions du vecteur {\ttfamily{a}} et le vecteur {\ttfamily{b}}.
    \item {\ttfamily{\textbf{prodVect(const V3 \& a, const V3 \& b)}}} : Renvoie le produit vectoriel du vecteur {\ttfamily{a}} et le vecteur {\ttfamily{b}}. 
\end{itemize}

\subsection{Visualisation 3D}

Afin de pouvoir mieux visualiser la représentation des positions des Ancres et des Tags dans le repère du Hub, nous avons mis en place un programme simple permettant de générer une image en trois dimensions de tous les points enregistrés par le Hub. Pour cela, nous avons utilisé la librairie externe {\ttfamily{<raylib.h>}} qui est téléchargeable depuis le web sur le terminal de commandes Linux. Nous l'avons utilisée pour implémenter notre programme de visualisation 3D dans notre librairie {\ttfamily{3DVisualisation.hpp}}.

\begin{figure}[!ht]
\centering 
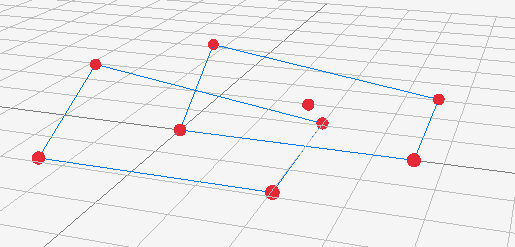
[picture p138: Rapport/Rapport projet/Figures/exemple_raylib.png]
 
\caption[calibrage Ancres de base]{Exemple d'affichage de points et de segments avec la librairie {\ttfamily{<raylib.h>}}}
\end{figure}

\subsection{Algorithme de Trilatération}

\begin{figure}[!ht]
\centering 
 
\caption[Illustration de la trilatération dans un espace en 3D]{Illustration de la trilatération dans un espace en 3D}
\end{figure}

Le choix de la technologie UWB ayant été effectué par notre équipe, nous savons donc que notre système est capable de récupérer les distances entre chaque ancre et chaque tag comportant un module UWB. Seulement, pour pouvoir répondre au cahier des charges que nous avons établi, notre système a besoin de pouvoir situer de la manière la plus précise et la plus conforme à la réalité la position relative de l'ouvrier par rapport au véhicule et à sa zone de sécurité.
C'est pourquoi nous avons effectué différentes recherches pour établir la liste des algorithmes existants qui seraient les plus aptes à répondre à notre problématique tout en étant capables d'exploiter au mieux les données récoltées par notre système. La technologie UWB existant depuis plusieurs décennies, nous avons donc pu obtenir une quantité importante d'articles traitant notre problème de calcul d'une position dans un repère en trois dimensions, et l'algorithme qui est le plus ressorti est celui de la Trilatération par la méthode des Moindres Carrés.

Le premier article de recherche ayant retenu notre attention est intitulé \emph{Lübeck University of Applied Sciences: Technical Report 2015} de Mathias Pelka \cite{trilateration_ref_1}. Ce court article se focalise principalement sur la résolution mathématique d'un système comportant les quatres équations des sphères ayant pour rayon la distance entre une des quatres ancres et le tag de l'ouvrier. Il fournit également un exemple d'implémentation de cet algorithme avec MATHLAB.

Le deuxième article intitulé \emph{UWB-Based Real-Time Indoor Positioning Systems: A
Comprehensive Review} \cite{trilateration_ref_2} détaille quant à lui les différentes méthodes pour effectuer la trilatération en incluant la méthode des moindres carrés, et explicite l'équation matricielle théorique finale découlant de la résolution du système d'équations établi dans le premier article, et que l'on obtient pour pouvoir calculer algorithmiquement les coordonnées d'un tag.

En ce qui concerne l'application de la méthode des Moindres Carrés pour obtenir l'équation matricielle que nous avons utilisée dans notre algorithme, nous nous sommes basés sur des extraits d'exemple d'application de la méthode sur des problèmes d'optimisation présentés par l'Université de Stanford et l'UCLA dans le document \emph{Introduction to Applied Linear Algebra – Vectors, Matrices, and Least Squares (Chapitre 8 : Least Squares)}\cite{trilateration_ref_3}. L'application du gradient sur l'équation matricielle d'origine est également détaillée dans un cours d'informatique du MIT intitulé \emph{Least squares and the normal equations} et rédigé par Alex Townsend\cite{trilateration_ref_4}.

\bigskip

Nous allons maintenant nous focaliser sur la résolution mathématique du problème pour pouvoir dégager une solution algorithme exploitable dans le cadre de notre système de détection fonctionnant à l'aide de quatres ancres et au moins un tag. Nous allons pour cela nous appuyer sur les démonstrations exposées dans les articles mentionnés précédemment.

\subsubsection{Définition des notions}

Étant donné que les modules UWB de Makerfabs nous permettent de récupérer les distances entre chaque ancre et le tag dont nous voulons connaître la position, et que nous pouvons obtenir les coordonnées de chaque ancre dans le repère virtuel du hub à l'aide de l'algorithme \emph{Multidimensional Scaling} (que nous aborderons par la suite), nous pouvons définir les notions suivantes :

\bigskip

Soit $i\in\ie{1}{4}$. On appelle $d_i$ la distance entre l'ancre $i$ et le tag de l'ouvrier. On attribue pour chaque ancre un triplet de coordonnées $(x_i, y_i, z_i)$ connues, et on note $(x, y, z)$ les coordonnées du tag ouvrier que l'on cherche à déterminer. On rappelle que l'équation d'une sphère de rayon $r$ et de centre $(x_0, y_0, z_0)$ est de la forme :

\begin{equation}
    (x-x_0)^2+(y-y_0)^2+(z-z_0)^2=r^2
\end{equation}

\subsubsection{Démonstration dans le cas théorique}

Étant donné que nous connaissons les distances entre chaque ancre et le tag dont on souhaite déterminer les coordonnées, on peut en déduire le système comportant les équations des quatres sphères de centre $(x_i, y_i, z_i)$ et de rayon $d_i$ et qui est vérifié par les coordonnées du tag $(x, y, z)$ :

\[
   \left\{
   \begin{aligned}
      (x-x_1)^2+(y-y_1)^2+(z-z_1)^2 &= d_1^2 \\
      (x-x_2)^2+(y-y_2)^2+(z-z_2)^2 &= d_2^2 \\
      (x-x_3)^2+(y-y_3)^2+(z-z_3)^2 &= d_3^2 \\
      (x-x_4)^2+(y-y_4)^2+(z-z_4)^2 &= d_4^2
   \end{aligned}
   \right.
\]

Nous nous retrouvons donc ici avec un système non linéaire surdéterminé. On peut dans un premier temps développer chaque équation et regrouper entre elles les variables qui rendent le système non linéaire :

\[
   \left\{
   \begin{aligned}
      (x^2 + y^2 + z^2) - 2xx_1 - 2yy_1 - 2zz_1 &= d_1^2 - x_1^2 - y_1^2 - z_1^2 \\
      (x^2 + y^2 + z^2) - 2xx_2 - 2yy_2 - 2zz_2 &= d_2^2 - x_2^2 - y_2^2 - z_2^2 \\
      (x^2 + y^2 + z^2) - 2xx_3 - 2yy_3 - 2zz_3 &= d_3^2 - x_3^2 - y_3^2 - z_3^2 \\
      (x^2 + y^2 + z^2) - 2xx_4 - 2yy_4 - 2zz_4 &= d_4^2 - x_4^2 - y_4^2 - z_4^2
   \end{aligned}
   \right.
\]

A partir de là, nous pouvons soustraire aux trois dernières lignes du système la première ligne pour linéariser celui-ci ($\forall i \in \ie{2}{4}, L_i=L_i-L_1$). On obtient donc après simplification et factorisation le système linéaire ci-contre :

\[
   \left\{
   \begin{aligned}
      2(x_2 - x_1)x + 2(y_2 - y_1)y + 2(z_2 - z_1)z = (x_2^2 + y_2^2 + z_2^2) - (x_1^2 + y_1^2 + z_1^2) - (d_2^2 - d_1^2) \\
      2(x_3 - x_1)x + 2(y_3 - y_1)y + 2(z_3 - z_1)z = (x_3^2 + y_3^2 + z_3^2) - (x_1^2 + y_1^2 + z_1^2) - (d_3^2 - d_1^2) \\
      2(x_4 - x_1)x + 2(y_4 - y_1)y + 2(z_4 - z_1)z = (x_4^2 + y_4^2 + z_4^2) - (x_1^2 + y_1^2 + z_1^2) - (d_4^2 - d_1^2) 
   \end{aligned}
   \right.
\]

En notant $X=$
$\begin{pmatrix}
    x \\
    y \\
    z
\end{pmatrix}$ et $A$ la matrice contenant les coefficients du membre gauche des équations, et $B$ la matrice contenant le membre de droite des équations du système, on obtient l'équation matricielle suivante :
\begin{equation}
    AX=B \Rightarrow X=A^{-1}B
\end{equation}

Cette équation nous permet donc de déterminer les coordonnées du tag par un simple calcul matriciel. Cependant, ce système admet une solution uniquement dans le cas où les distances $d_i$ qui ont été mesurées sont exactes. Or nos distances ayant été mesurées par des modules UWB qui possèdent une certaine incertitude sur leur mesure en fonction de leur calibrage, l'utilisation de cette équation n'est pas envisageable dans un cas pratique comme le nôtre où les mesures risquent d'être souvent inexactes.

La seconde solution s'offrant à nous est donc d'introduire une matrice de bruit $R$ tel que :

\begin{equation}
    R=AX-B
\end{equation}

Cette équation peut être résolue en utilisant la méthode des \emph{Moindres Carrés} que nous allons détailler dans la partie suivante.

\subsubsection{Méthode des Moindres Carrés}

Pour pouvoir réduire au maximum les incertitudes liées aux mesures de nos distances $d_i$ effectuées par les modules UWB, nous pouvons dans un premier temps construire un système de 6 équations à 3 inconnues formées à partir des équations du précédent système, et de la forme suivante :

\[
   \left\{
   \begin{aligned}
      L_1 - L_2 \\
      L_1 - L_3 \\
      L_1 - L_4 \\
      L_2 - L_3 \\
      L_2 - L_4 \\
      L_3 - L_4 
   \end{aligned}
   \right.
\]

En repassant dans le domaine matriciel, on peut réécrire à nouveau les matrices $A$ et $B$, avec cette fois-ci $A$ de taille $6 \times 3$ et $B$ un vecteur de taille $6 \times 1$, de la manière suivante : 

\bigskip

$A = \begin{pmatrix}
   2(x_2 - x_1) & 2(y_2 - y_1) & 2(z_2 - z_1) \\
   2(x_3 - x_1) & 2(y_3 - y_1) & 2(z_3 - z_1) \\
   2(x_4 - x_1) & 2(y_4 - y_1) & 2(z_4 - z_1) \\
   2(x_3 - x_2) & 2(y_3 - y_2) & 2(z_3 - z_2) \\
   2(x_4 - x_2) & 2(y_4 - y_2) & 2(z_4 - z_2) \\
   2(x_4 - x_3) & 2(y_4 - y_3) & 2(z_4 - z_3)
\end{pmatrix}$
$B = \begin{pmatrix}
   (x_2^2 + y_2^2 + z_2^2) - (x_1^2 + y_1^2 + z_1^2) - (d_2^2 - d_1^2) \\
   (x_3^2 + y_3^2 + z_3^2) - (x_1^2 + y_1^2 + z_1^2) - (d_3^2 - d_1^2) \\
   (x_4^2 + y_4^2 + z_4^2) - (x_1^2 + y_1^2 + z_1^2) - (d_4^2 - d_1^2) \\
   (x_3^2 + y_3^2 + z_3^2) - (x_2^2 + y_2^2 + z_2^2) - (d_3^2 - d_2^2) \\
   (x_4^2 + y_4^2 + z_4^2) - (x_2^2 + y_2^2 + z_2^2) - (d_4^2 - d_2^2) \\
   (x_4^2 + y_4^2 + z_4^2) - (x_3^2 + y_3^2 + z_3^2) - (d_4^2 - d_3^2)
\end{pmatrix}$

\bigskip

A partir de l'équation matricielle $(4)$ introduite précédemment, nous allons maintenant appliquer la méthode des \emph{Moindres Carrés}. Cette méthode consiste à minimiser la somme des carrés des écarts afin que les coordonnées calculées soient le plus proches possible des coordonnées réelles du tag. Si l'on note pour tout $i \in \ie{1}{6}, r_i$ les coefficients du vecteur $R$ de taille $6 \times 1$, on peut poser la fonction de coût suivante :

\begin{equation}
   S(X) = \sum_{i=1}^{6} r_i^2 \Rightarrow S(X)=RR^T
\end{equation}

On peut traduire cette équation dans le domaine matriciel : 

\begin{equation}
   S(X)=(AX - B)^T (AX - B)
\end{equation}

On peut ensuite développer cette équation :

\begin{equation}
   \Rightarrow S(X) = (X^T A^T - B^T)(AX - B)
\end{equation}

\begin{equation}
   \Rightarrow S(X) = X^T A^T A X - X^T A^T B - B^T A X + B^T B
\end{equation}

Comme $X^T A^T B$ est un nombre scalaire (une matrice de taille $1 \times 1$), il est égal à sa propre transposée. On a donc $(X^T A^T B)^T = B^T A X$. On obtient donc l'équation suivante : 

\begin{equation}
   \Rightarrow S(X) = X^T A^T A X - 2 X^T A^T B + B^T B
\end{equation}

Étant donné que l'objectif consistait à l'origine à minimiser $S(X)$, nous allons donc chercher à déterminer la solution de l'équation $\nabla S(X)=0$. On en déduit l'équation matricielle suivante :

\begin{equation}
   \Rightarrow \nabla_X S(X) = 2 A^T A X - 2 A^T B
\end{equation}

\begin{equation}
   \Rightarrow 2 A^T A X - 2 A^T B = 0 \implies A^T A X = A^T B
\end{equation}

On peut ensuite isoler $X$ pour en déduire les coordonnées finales du tag ouvrier : 

\begin{equation}
   X = (A^T A)^{-1} A^T B
\end{equation}

\subsubsection{Implémentation de l'algorithme}

Pour pouvoir mettre en oeuvre cet algorithme dans le code de notre projet, nous avons créé la librairie {\ttfamily{Trilateration.h}}. Cette librairie utilise la librairie {\ttfamily{Eigen}} qui est spécialement optimisée pour les calculs matriciels en {\ttfamily{C++}} afin de limiter la complexité temporelle et spatiale de ces calculs. Notre librairie {\ttfamily{Trilateration.h}} contient donc les fonctions suivantes :

\begin{itemize}
   \item {\ttfamily{initMatrixA()}} : Cette fonction initialise la matrice $A$ de l'équation $(13)$ dans la variable globale {\ttfamily{gA}}.
   \item {\ttfamily{initMatrixB()}} : Cette fonction initialise la matrice $B$ de l'équation $(13)$ dans la variable globale {\ttfamily{gB}}.
   \item {\ttfamily{trilateration3D(UWBModuleList \& pAnchors,\allowbreak unordered\_map<int, float> pDistances)}} : Cette fonction renvoie des coordonnées de type {\ttfamily{V3}} correspondant au tag dont l'on veut connaître la position.
\end{itemize}

Nous venons donc de voir la méthode utilisée par notre système pour déterminer la position exacte du tag dans le repère virtuel du hub. Cependant, comme précisé dans l'introduction de la méthode, nous avons besoin de connaître les coordonnées de chaque ancres $(x_i, y_i, z_i)$ dans le repère virtuel du hub. Pour que les distances entre les ancres sur le véhicule de chantier correspondent avec les distances entre les ancres dans le repère virtuel du hub, nous devons donc implémenter un algorithme chargé de déterminer les coordonnées de chaque ancre. C'est ce que nous allons donc aborder dans la partie suivante.

\subsection{Algorithme de Multidimensional Scaling}

L'algorithme de \emph{Multidimensional Scaling} consiste pour résumer à appliquer l'algorithme de la descente de gradient en prenant comme fonction de coût la fonction \emph{Stress} dont l'élaboration et l'utilisation sont explicitées par le mathématicien J. B. KRUSKAL dans son article paru en 1964 intitulé \emph{Multidimensional scaling by optimizing goodness of fit to a nonmetric hypothesis}\cite{mds_ref_1}. Un résumé de l'ensemble des recherches autour de cet algorithme a été élaboré dans l'article intitulé \emph{The Past, Present, and Future of Multidimensional Scaling}, coécrit par Patrick J.F. Groenen et Ingwer Borg et paru en 2013\cite{mds_ref_2}. 

Pour résumer, l'objectif de cet algorithme au sein de notre système est de déterminer, à chaque itération de celui-ci, si les distances entre chaque ancre calculées à l'aide des coordonnées des ancres du repère virtuel stocké dans le hub correspondent bien aux distances mesurées par les modules UWB des ancres. Si ce n'est pas le cas, l'algorithme va légèrement modifier les positions de chaque ancre dans le repère du hub pour que les distances calculées par le hub se rapprochent le plus possible des distances réelles entre les ancres.

Nous allons dans un premier temps définir les notions liées à l'algorithme avant d'expliciter les procédés mathématiques qui y sont utilisés.

\subsubsection{Définition des notions}

\begin{definition}
   Soit $X = [X_1, X_2, X_3, X_4]^T$ la matrice contenant les coordonnées 3D des quatres ancres, tel que pour tout $ (i,j) \in \ie{1}{4}^2, X_i = (x_i, y_i, z_i) \in \mathbb{R}^3$. Notons $d_{ij}$ la distance mesurée entre l'ancre $i$ et l'ancre $j$, et $\hat{d}_{ij}(X)$ la distance euclidienne calculée à partir des coordonnées actuelles. Alors on définit $\hat{d}_{ij}(X)$ tel que :
   
   $$\hat{d}_{ij}(X) = \|X_i - X_j\|_2 = \sqrt{(x_i - x_j)^2 + (y_i - y_j)^2 + (z_i - z_j)^2}$$
\end{definition}

\begin{definition}
   On appelle fonction de \emph{Stress} la fonction $E:M_{4,3}(\mathbb{R})\rightarrow\mathbb{R}$ et qui est définie par :

   $$E(X) = \frac{1}{2} \sum_{i=1}^{4} \sum_{j \neq i} \left( \hat{d}_{ij}(X) - d_{ij} \right)^2$$

   Cette fonction correspond à la fonction de coût que nous allons utiliser par la suite pour la descente de gradient.
\end{definition}

\subsubsection{Descente de gradient}

Afin de pouvoir appliquer l'algorithme de la descente de gradient pour l'algorithme du \emph{Multidimensional Scaling}, nous devons dans un premier temps calculer le gradient de la fonction de coût choisie, qui est donc ici la fonction de \emph{Stress}. En appliquant les règles de dérivation des fonctions composées, on obtient l'équation suivante :

$$\nabla_{X_i} E(X) = \sum_{j \neq i} \left( \hat{d}_{ij}(X) - d_{ij} \right) \cdot \nabla_{X_i} \hat{d}_{ij}(X)$$

On peut ensuite calculer le gradient par rapport à $X_i$ de la distance $\hat{d}_{ij}(X)$ calculée par le hub :

$$\nabla_{X_i} \hat{d}_{ij}(X) = \nabla_{X_i} \|X_i - X_j\|_2 = \frac{X_i - X_j}{\|X_i - X_j\|_2}$$

On injecte le résultat dans l'équation d'origine, ce qui nous donne l'équation finale suivante : 

\begin{equation}
   \nabla_{X_i} E(X) = \sum_{j \neq i} \left( \hat{d}_{ij}(X) - d_{ij} \right) \cdot \frac{X_i - X_j}{\|X_i - X_j\|_2}
\end{equation}

Soient $n \in \mathbb{N}$ le nombre d'itérations effectuées par l'algorithme de la descente de gradient et $\alpha \in \mathbb{R}$ la vitesse d'apprentissage de l'algorithme. Pour tout $k \in \ie{1}{n}$, $X_i^{(k)}$ correspond à la valeur de $X_i$ à la $k$-ième itération. L'algorithme applique donc en boucle pour chaque ensemble de coordonnées, en fonction du nombre d'itérations passé en paramètre, le calcul présenté ci-dessous : 

$$X_i^{(k+1)} = X_i^{(k)} - \alpha \cdot \nabla_{X_i} E(X^{(k)})$$

\subsubsection{Implémentation de l'algorithme}

Afin de simplifier les calculs effectués par l'ESP32-WROVER-E du hub lors de l'exécution de l'algorithme, nous avons réécrit l'équation $(13)$ de la manière suivante dans notre programme :

$$\nabla_{X_i} E(X) = \sum_{j \neq i} (X_i - X_j) \cdot \left( \frac{\hat{d}_{ij}(X) - d_{ij}}{\hat{d}_{ij}(X)} \right)$$

Nous avons donc utilisé cette équation dans notre programme implémentant l'algorithme de \emph{Multidimensional Scaling}, avec comme paramètres $n=1000$ et $\alpha=0.01$. Nous avons créé la librairie {\ttfamily{GridLibrary.hpp}} dans laquelle nous avons implémenté l'algorithme dans la fonction {\ttfamily{initAnchors\allowbreak CoordinatesWithGD}}.

Voici un exemple visuel du résultat de l'algorithme lors de son utilisation pour le placement des ancres pendant le \uline{Jour des Projet} de l'ESIEE Paris :

\begin{figure}[!ht]
\centering 
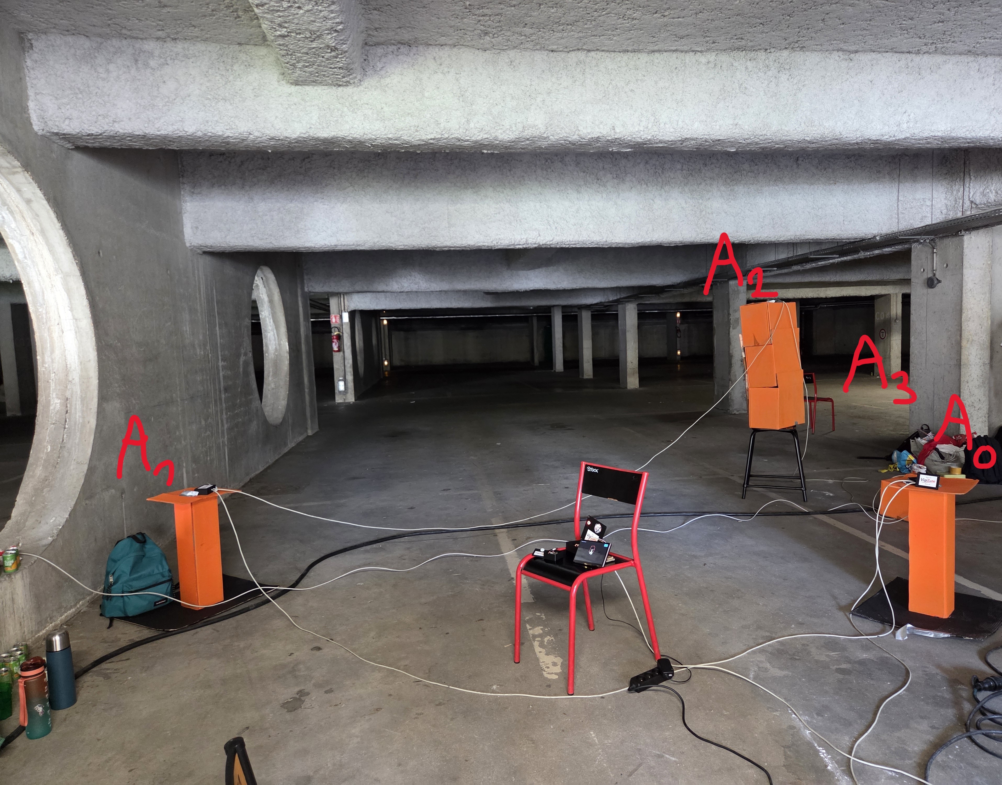
[picture p139: Rapport/Rapport projet/Figures/placement_ancres_jdp.jpg]
 
\caption[Calibrage des Ancres JDP]{Placement réelle des ancres lors du \uline{Jour des Projets}}
\end{figure}

\begin{figure}[!ht]
\centering 
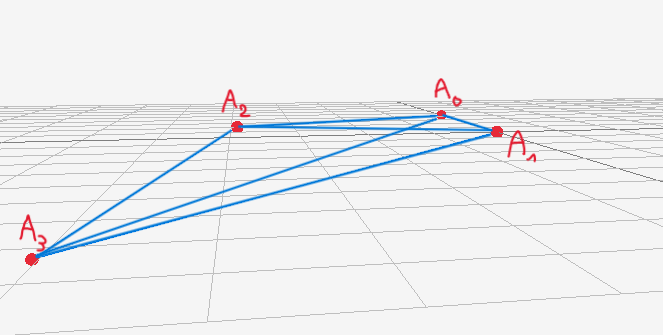
[picture p140: Rapport/Rapport projet/Figures/calibrage_ancres.png]
 
\caption[Calibrage des Ancres JDP (repère virtuel)]{Reconstitution de la position des ancres par l'algorithme de \emph{Multidimensional Scaling}}
\end{figure}

Comme évoqué précédemment, l'algorithme de \emph{Multidimensional Scaling} a besoin de connaître les distances entre chaque ancre pour pouvoir effectuer la descente de gradient. Nous avons donc écrit dans un premier temps un algorithme permettant de récupérer les distances entre chaque ancre en exécutant la méthode suivante en boucle :

\bigskip

\textbf{Pour les ancres :}

\begin{itemize}
   \item On vérifie si le Hub nous a envoyé un message pour nous avertir que la phase d'initialisation de la position des ancres est terminée. Si c'est le cas, on arrête le programme d'initialisation, sinon on lance la phase d'initialisation suivante : 
   \item \begin{itemize}
      \item On attend de recevoir un signal du hub pour nous indiquer que l'on doit se transformer en tag.
      \item Si on s'est transformé en tag : 
      \item \begin{itemize}
         \item On vérifie que le hub ne nous a pas demandé de nous transformer en ancre. Si on a bien reçu un message, on arrête la phase courante d'initialisation et on repasse en mode ancre. Sinon, on effectue l'action ci dessous : 
         \item On envoie la distance entre nous et la seule ancre toujours en mode ancre sur les quatres (l'ancre statique)
      \end{itemize}
   \end{itemize}
\end{itemize}

\bigskip

\textbf{Pour le hub :}

\begin{itemize}
   \item On envoie un message à toutes les ancres pour signifier que la phase d'initialisation de la position des ancres commence.
   \item On définit à tour de rôle une ancre statique, et on envoie un message aux trois autres pour qu'elle passe en mode tag.
   \item On attend de recevoir un tableau contenant les 3 distances entre chaque ancre.
\end{itemize}

Cependant, la précision des mesures des distances entre les ancres n'ayant pas été très pointue lors de nos premiers tests (le taux d'erreurs pour les mesures oscillait entre 25\% et 50\%), nous avons pour le moment décidé de proposer à l'utilisateur de saisir manuellement les distances entre chaque ancre. L'algorithme de collecte des distances dépicté ci-dessus nécessiterait une phase de développement plus importante avant d'envisager son utilisation au sein de notre système.

\bigskip

Nous avons donc explicité dans cette partie l'algorithme de \emph{Multidimensional Scaling} permettant d'initialiser les positions des ancres au sein du repère virtuel du hub. Nous étudierons par la suite l'algorithme de modélisation et de lissage de la zone de sécurité. Cependant, cet algorithme ayant également comme tâche la transmission des coordonnées des points formant la zone de sécurité dans un repère en deux dimensions à l'écran, il est nécessaire d'effectuer une projection des coordonnées 3D des points dans un repère en deux dimensions. Afin d'éviter l'exécution systématique d'un algorithme de projection des points sur le plan $(\vec{x}, \vec{y})$ du repère virtuel du hub, nous avons préféré écrire un algorithme de changement de base non seulement afin de limiter le temps de calcul de la fonction de projection, mais aussi dans le but de simplifier les programmes d'échanges de données entre le hub et l'écran. Nous allons donc étudier cet algorithme de changement de base dans la partie suivante.

\subsection{Algorithme de changement de repère}

Comme introduit précédemment, nous avons besoin de l'algorithme de changement de base à la fois pour réduire le temps de calcul de la fonction de projection et à la fois pour simplifier les échanges de données entre le hub et l'écran. Étant donné que nous comptions également mettre les ancres ainsi que la représentation du véhicule équipé de notre système au centre de l'écran, nous avons besoin non seulement que le repère virtuel du hub soit exactement le repère du plan du véhicule, mais également que l'épicentre des ancres se situe au centre de notre repère afin de pouvoir aisément les afficher au centre de l'écran. C'est pour cette raison que nous avons réparti l'algorithme de changement de repère en deux parties :

\begin{itemize}
   \item {\ttfamily \textbf{giveEpicenterPosition}} : Calcule et renvoie les coordonnées de l'épicentre des ancres qui correspond au vecteur utilisé pour la translation des ancres vers l'origine du repère tel que leur nouvel épicentre ait pour coordonnées $(0, 0, 0)$. La fonction renvoie donc $\frac{\sum_{i=1}^{4}X_i}{4}$.
   \item {\ttfamily \textbf{changeCoordinateSystem}} : Calcule la matrice utilisée pour le changement de base et applique celui-ci sur tous les points passés en paramètre de la fonction.
\end{itemize}

Nous allons donc ici détailler brièvement l'algorithme utilisé pour le changement de base de tous les points enregistrés dans le repère virtuel du hub dans la fonction {\ttfamily \textbf{changeCoordinateSystem}}.

\subsubsection{Démonstration}

Afin d'effectuer un changement de repère pour passer du repère basé sur le plan des ancres au repère du plan de la zone de sécurité (qui est donc le plan du véhicule), nous avons besoin de connaître le vecteur normal à ce plan qui constituera l'axe $Z$ de notre nouvelle base. Nous pouvons construire ce vecteur à partir des coefficients $(a, b, c)\in \mathbb{R}^3$ de l'équation du plan de la zone de sécurité, dont l'obtention sera précisée dans la partie \emph{Modélisation et lissage de la zone de sécurité}.

Soit $n=$$\begin{pmatrix}
    a \\
    b \\
    c
\end{pmatrix}$ le vecteur normal au plan de la zone de sécurité. Nous pouvons tout simplement définir le vecteur directeur $w$ de l'axe $Z$ tel que :

$$w=\frac{n}{\norme{n}_2}$$

Pour créer le second vecteur de la base, il nous suffit de prendre un vecteur arbitraire non-colinéaire à $w$ puis de calculer le produit vectoriel des deux vecteurs. Pour ce faire, on définit le vecteur $t$ de la manière suivante : 

\[
t = 
\begin{cases}
   (1, 0, 0) & \text{si } |w_x| < 0.9 \\
   (0, 1, 0) & \text{sinon}
\end{cases}
\]

On calcule ensuite le vecteur directeur $u$ de l'axe $X$ :

$$u=\frac{t \wedge w}{\norme{t \wedge w}}$$

On peut donc enfin déterminer le vecteur $v$ de l'axe $Y$ à l'aide des deux vecteurs précédents :

$$v=\frac{w \wedge u}{\norme{w \wedge u}}$$

On peut donc en déduire la matrice de changement de base suivante :

$$M=\begin{pmatrix}
   u_x & u_y & u_z \\
   v_x & v_y & v_z \\
   w_x & w_y & w_z
\end{pmatrix}$$

Pour obtenir les nouvelles coordonnées $X'$ d'un point $X$ dans notre nouvelle base, il suffit d'effectuer le calcul ci-dessous :

$$X'=MX$$

\subsubsection{Implémentation de l'algorithme}

L'algorithme de changement de repère final que nous avons implémenté dans notre système se structure donc de la manière suivante :

\begin{itemize}
   \item On déplace l'épicentre des ancres aux coordonnées $(0, 0, 0)$ à l'aide de la fonction {\ttfamily \textbf{giveEpicenterPosition}}.
   \item On lance le programme de \emph{Modélisation et lissage de la zone de sécurité} pour pouvoir récupérer les coordonnées des points constituants la zone de sécurité.
   \item On applique la fonction de changement de base {\ttfamily \textbf{changeCoordinateSystem}} sur tous les points composant la zone de sécurité ainsi que les ancres.
\end{itemize}

Nous pouvons voir l'exécutions de ces différentes étapes à travers les images ci-contre :

\begin{figure}[!ht]
\centering 
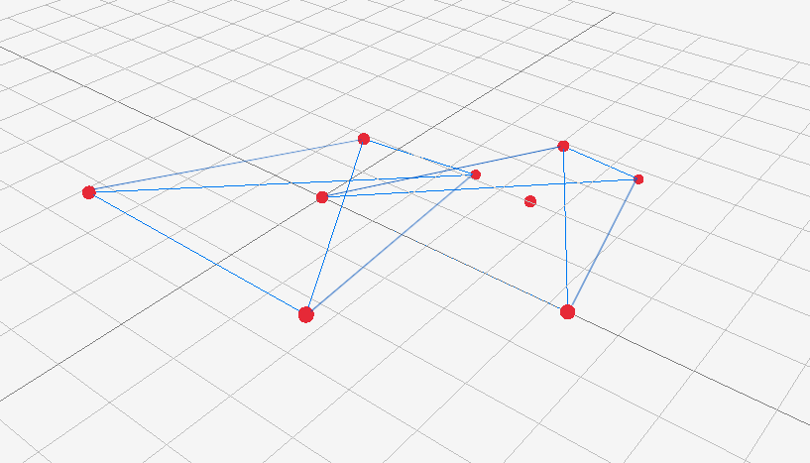
[picture p141: Rapport/Rapport projet/Figures/chgt_base_1.png]
 
\caption[Translation de l'épicentre des ancres]{Translation de l'épicentre des ancres en $(0, 0, 0)$}
\end{figure}

\begin{figure}[!ht]
\centering 
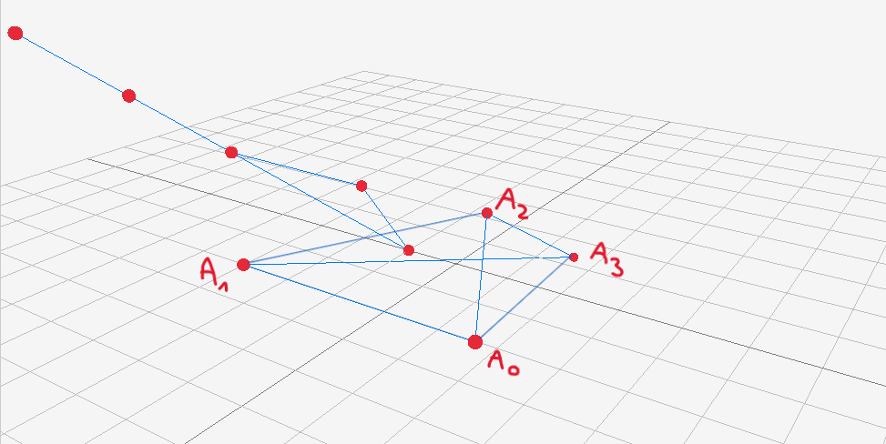
[picture p142: Rapport/Rapport projet/Figures/chgt_base_2.png]
 
\caption[Repère virtuel du hub avant le changement de base]{Repère virtuel du hub avant le changement de base}
\end{figure}

\begin{figure}[!ht]
\centering 
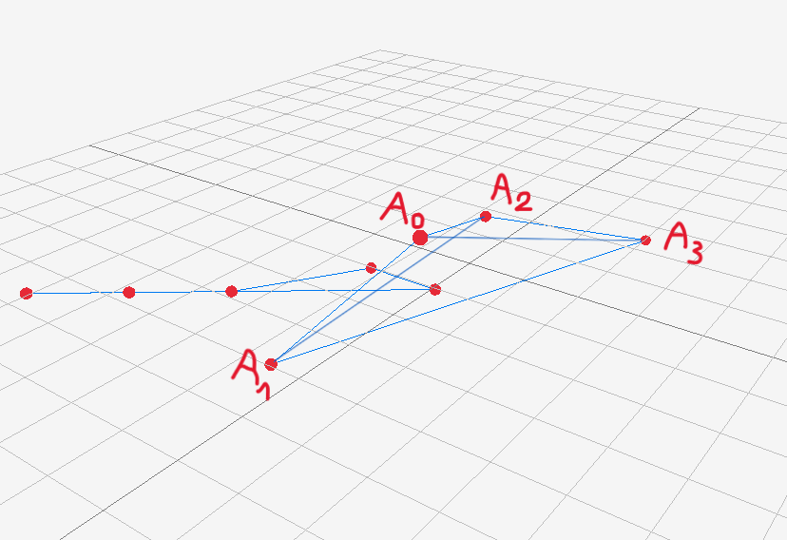
[picture p143: Rapport/Rapport projet/Figures/chgt_base_3.png]
 
\caption[Repère virtuel du hub après le changement de base]{Repère virtuel du hub après le changement de base}
\end{figure}

\newpage

Nous allons maintenant expliciter le déroulement de l'algorithme utilisé par le hub afin de modéliser une zone de sécurité qu'il peut utiliser pour calculer la distance entre un tag et celle-ci et qu'il peut transmettre à l'écran pour que celui-ci puisse afficher des informations utiles au conducteur du véhicule.
