maxime-leblan/Projet-E3-2026-ESIEE-Paris/Rapport/Exemple de document LateX/TIPE_MPI_2025___Sécurisation_réseau_ordinateurs/graphe_sha.png

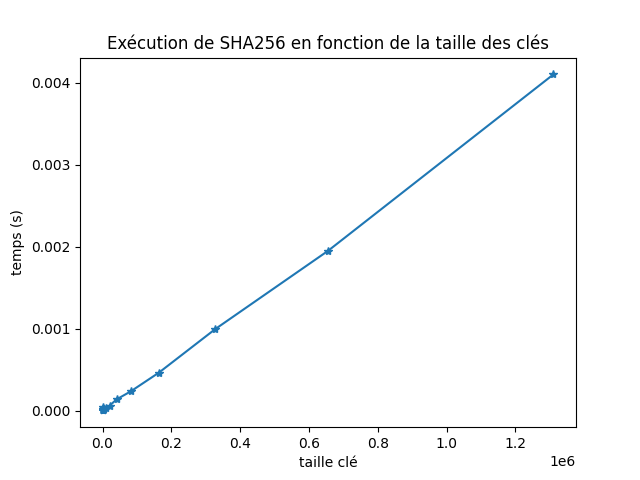
Rapport/Exemple de document LateX/TIPE_MPI_2025___Sécurisation_réseau_ordinateurs/graphe_sha.png
