maxime-leblan/Projet-E3-2026-ESIEE-Paris/Rapport/Exemple de document LateX/TIPE_MPI_2025___Sécurisation_réseau_ordinateurs/hach_1.png

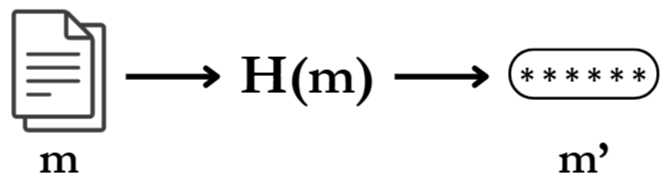
Rapport/Exemple de document LateX/TIPE_MPI_2025___Sécurisation_réseau_ordinateurs/hach_1.png
