maxime-leblan/Projet-E3-2026-ESIEE-Paris/Rapport/Rapport projet/Figures/2N222_complete.png

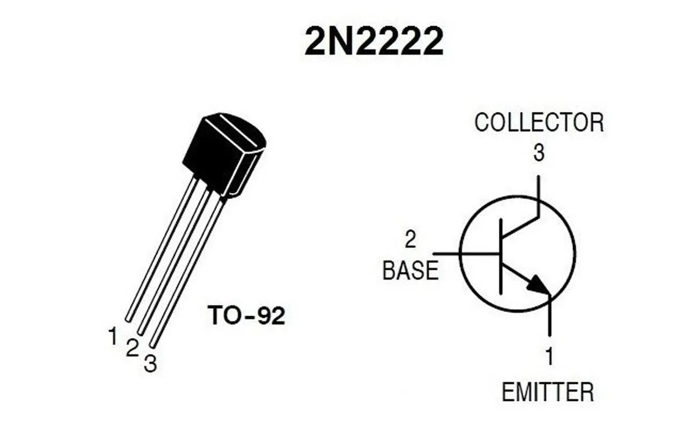
Rapport/Rapport projet/Figures/2N222_complete.png
