maxime-leblan/Projet-E3-2026-ESIEE-Paris/Rapport/Rapport projet/Figures/buzzer_piezzo_both_view.png

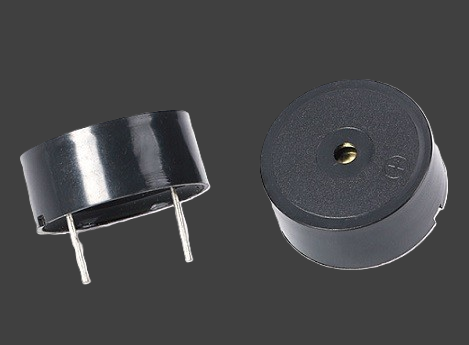
Rapport/Rapport projet/Figures/buzzer_piezzo_both_view.png
