maxime-leblan/Projet-E3-2026-ESIEE-Paris/Rapport/Rapport projet/Figures/carte-ouvrier-pasfini.jpg

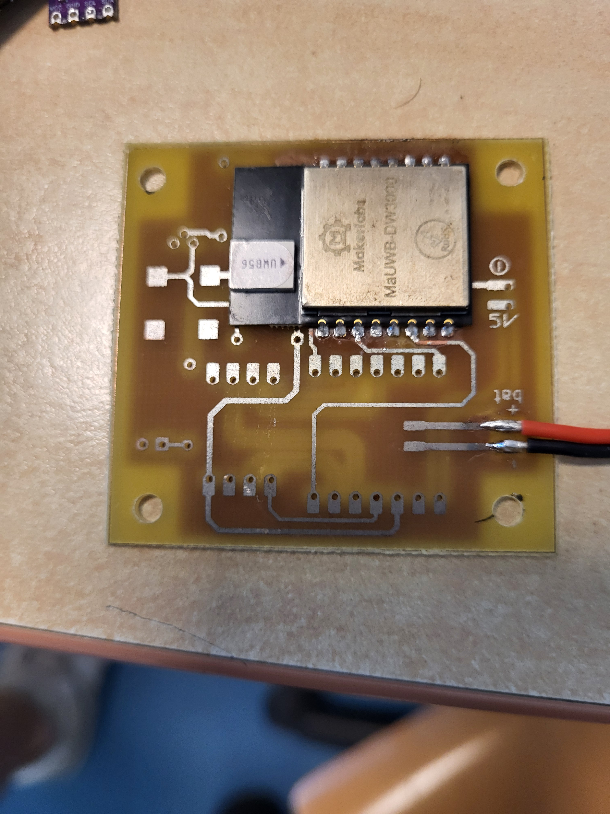
Rapport/Rapport projet/Figures/carte-ouvrier-pasfini.jpg
