maxime-leblan/Projet-E3-2026-ESIEE-Paris/Rapport/Rapport projet/Figures/chantier3.png

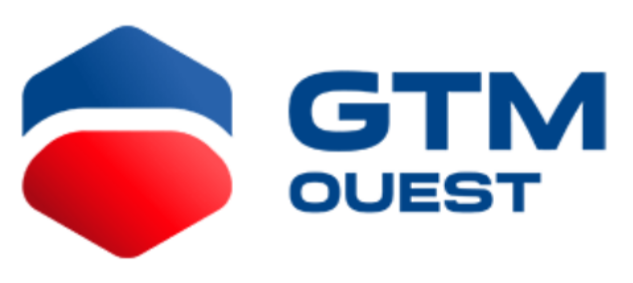
Rapport/Rapport projet/Figures/chantier3.png
