maxime-leblan/Projet-E3-2026-ESIEE-Paris/Rapport/Rapport projet/Figures/Chantier8.jpg

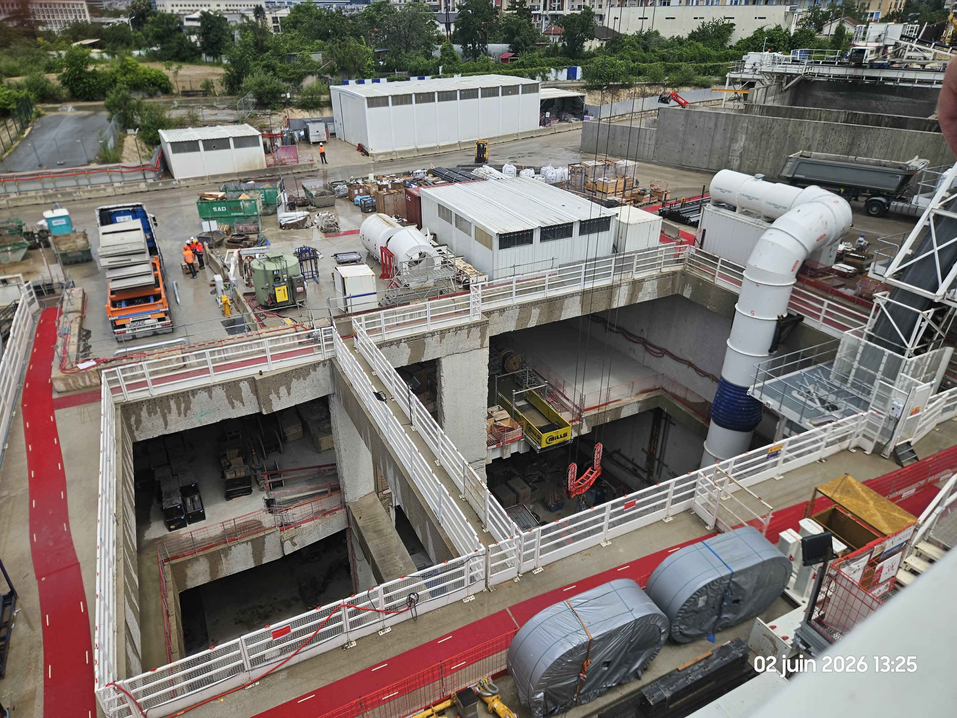
Rapport/Rapport projet/Figures/Chantier8.jpg
