maxime-leblan/Projet-E3-2026-ESIEE-Paris/Rapport/Rapport projet/Figures/Chantier10.jpg

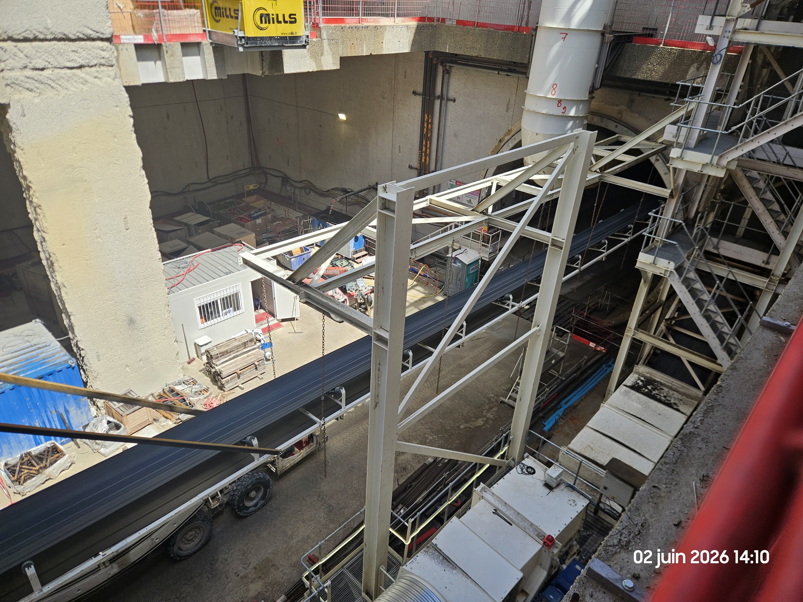
Rapport/Rapport projet/Figures/Chantier10.jpg
