maxime-leblan/Projet-E3-2026-ESIEE-Paris/Rapport/Rapport projet/Figures/photo_groupe.png

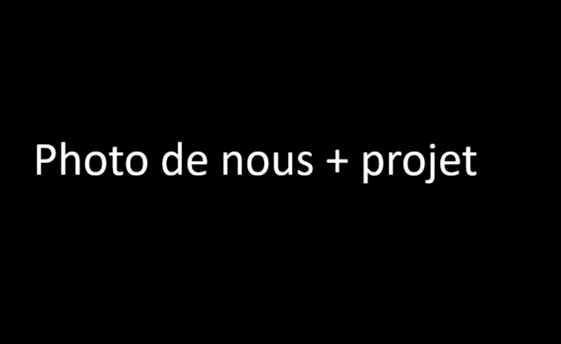
Rapport/Rapport projet/Figures/photo_groupe.png
