maxime-leblan/Projet-E3-2026-ESIEE-Paris/Rapport/Rapport projet/Figures/systeme_buzzer.png

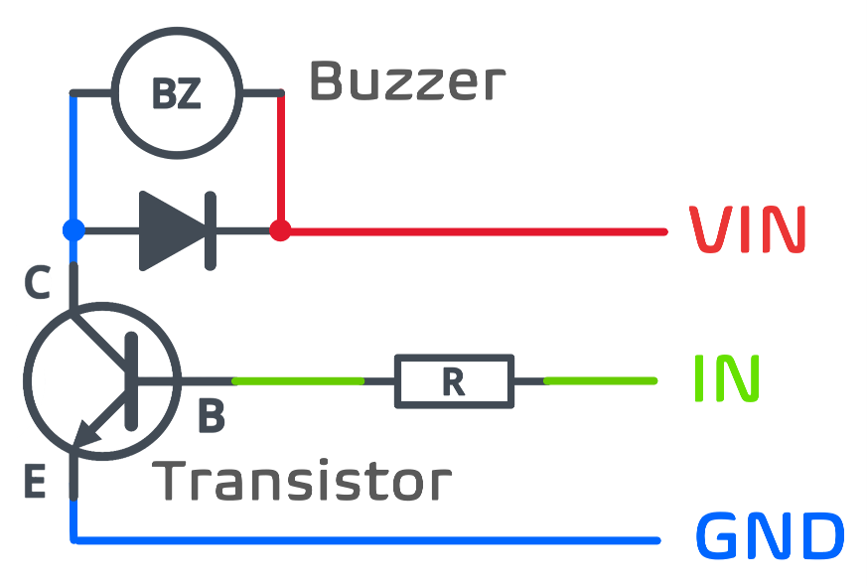
Rapport/Rapport projet/Figures/systeme_buzzer.png
