maxime-leblan/Projet-E3-2026-ESIEE-Paris/Rapport/Rapport projet/Figures/carte-hub.jpg

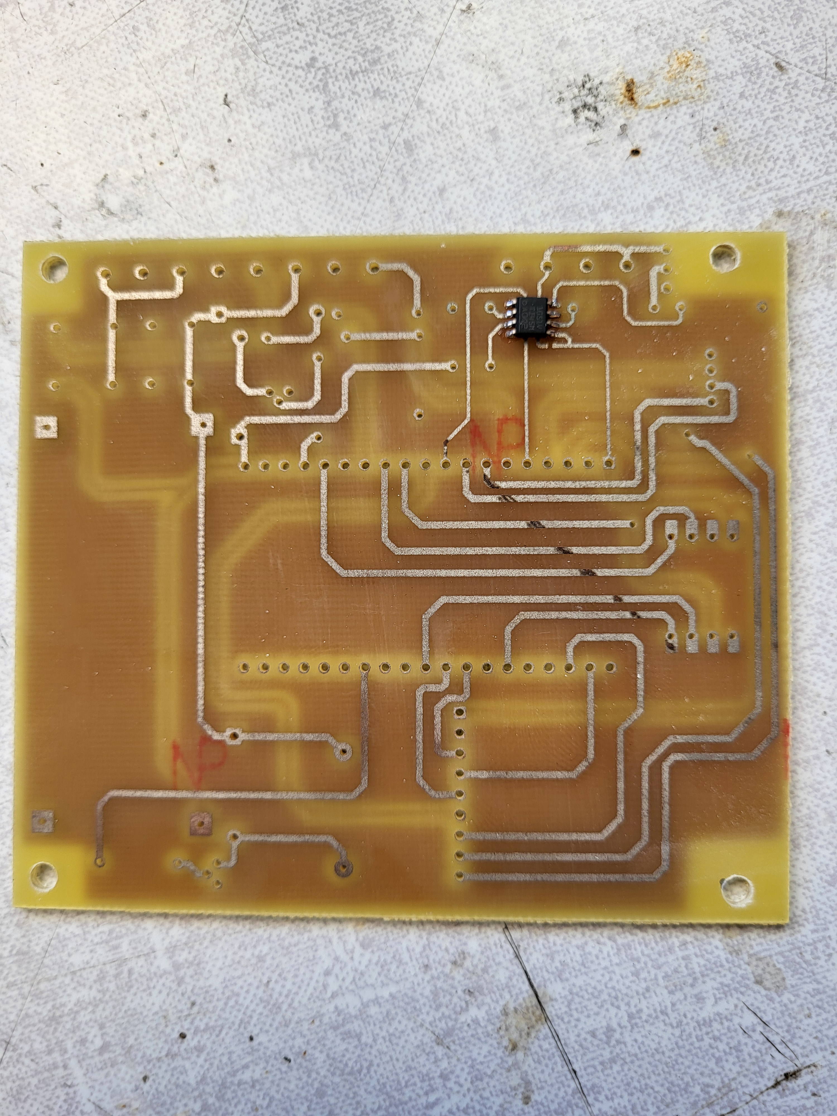
[picture p51: Rapport/Rapport projet/Figures/carte-hub.jpg]
Rapport/Rapport projet/Figures/carte-hub.jpg
