maxime-leblan/Projet-E3-2026-ESIEE-Paris/Rapport/Rapport projet/Figures/soudure-benoit.jpg

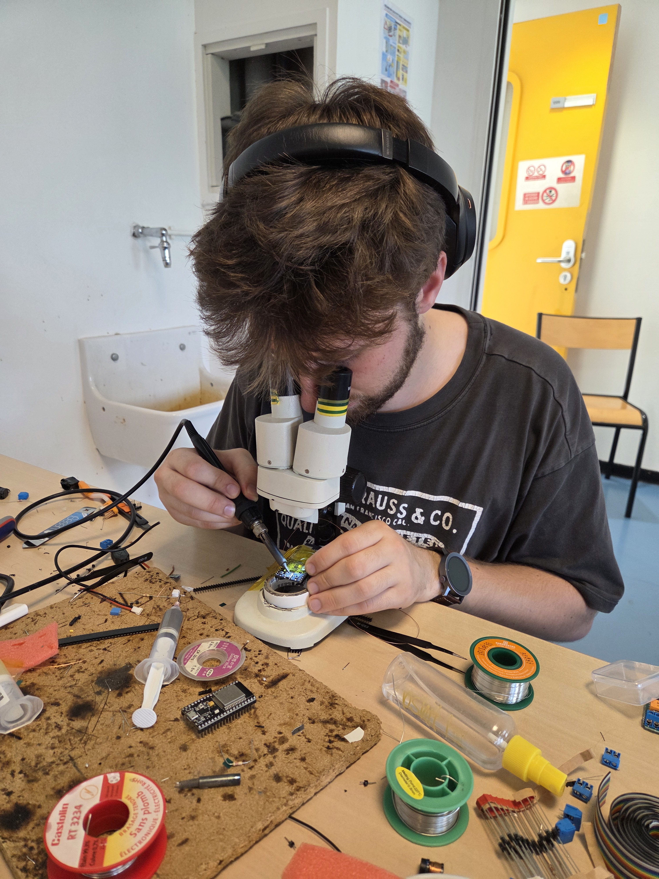
[picture p54: Rapport/Rapport projet/Figures/soudure-benoit.jpg]
Rapport/Rapport projet/Figures/soudure-benoit.jpg
