maxime-leblan/Projet-E3-2026-ESIEE-Paris/Rapport/Rapport projet/Figures/percages-colonne.jpg

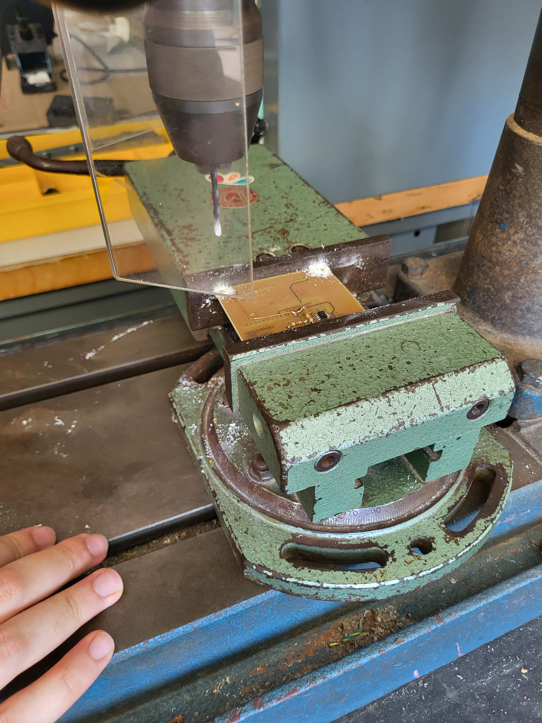
[picture p59: Rapport/Rapport projet/Figures/percages-colonne.jpg]
Rapport/Rapport projet/Figures/percages-colonne.jpg
