maxime-leblan/Projet-E3-2026-ESIEE-Paris/Rapport/Rapport projet/Figures/carte-hub-fini.jpg

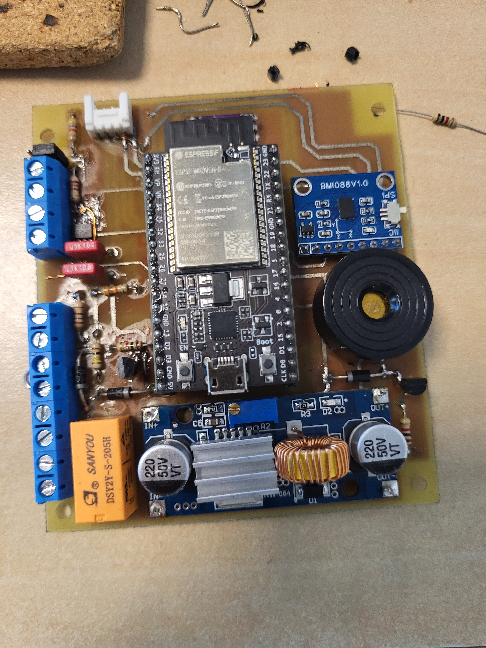
Rapport/Rapport projet/Figures/carte-hub-fini.jpg
