maxime-leblan/Projet-E3-2026-ESIEE-Paris/Rapport/Rapport projet/Figures/percages-colonne-carte.jpg

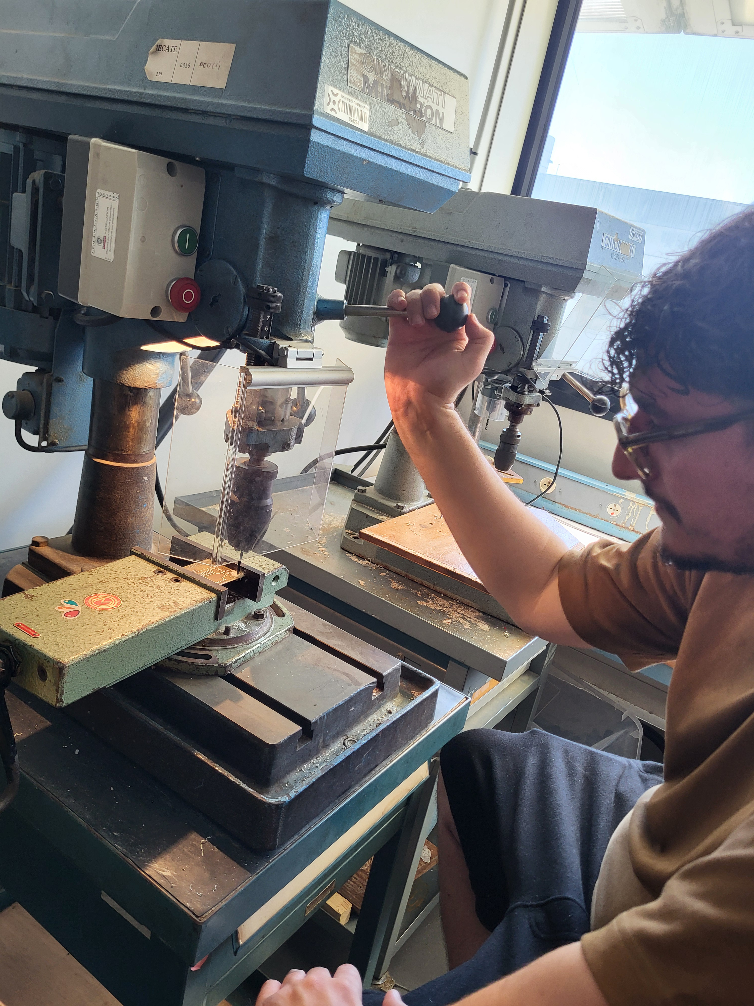
Rapport/Rapport projet/Figures/percages-colonne-carte.jpg
